ozcanyardimci/IoT_gateway/docs/subsystems/rs232.md

# RS232 Subsystem — Build Plan

**Status:** DONE, all 8 plan steps closed 2026-09-10. ERC deliberately not run before
closing the doc — project moved to a single end-of-project ERC pass across all
subsystems (Ozcan's decision, same approach `status-indication.md` already used) rather
than the per-subsystem pre-merge policy earlier subsystems followed. Tracked in
`CLAUDE.md` Open items.

## Scope

One point-to-point RS232 serial port on IOBOARD: TXD/RXD only, referenced to `GND_LOGIC`
(this port is **not** isolated — already fixed in `power.md`'s isolation table: "RS232 |
No | MAX3232E has no isolation"). No hardware flow control lines (RTS/CTS/DTR/DSR/etc.) —
same reasoning already applied project-wide: this project only ever wired TX/RX for its
UART-based interfaces. No DE/RE — that's an RS485-specific half-duplex control signal,
not applicable here. Not in scope: RS485 (separate subsystem, already complete), PCB
layout, DTE/DCE cable-adapter conventions for whatever gets plugged into the field side.

## Design approach

Four decisions, in the order they were made:

1. **Transceiver: TI MAX3232EIPWR (TSSOP-16, tape & reel, -40 to +85°C), one channel
   used.** Corrected 2026-09-10 from an earlier placeholder "MAX3232EI" that was never a
   real orderable part by itself — it's Texas Instruments' industrial-temp *family
   prefix*, not a buyable SKU (needs a package suffix: EID/EIDB/EIDW/EIPW, each with an
   optional R for tape-and-reel). Landed on TI's part specifically, not Analog
   Devices/Maxim's equivalent (MAX3232EEUE+), because TI's is the one with a ready
   SnapEDA symbol/footprint — practical, not electrical: pinout and function are
   identical either way, same classic second-sourced part. Datasheet switched to match:
   TI's own MAX3232E datasheet, not ADI/Maxim's. The MAX3232E family itself has been the
   standing choice for this project since before this doc existed (`architecture.md`,
   `power.md`) — a 3.3V-native RS232 transceiver, consistent with the `3V3_LOGIC` rail
   everything else on this board runs from. Full datasheet obtained and confirmed
   2026-09-10 ([TI MAX3232E
   datasheet](https://www.ti.com/lit/ds/slls664c/slls664c.pdf)): 16-pin part, two
   independent driver/receiver channels. This design only needs one RS232 signal pair
   (TXD/RXD), so channel 1 (DIN1/DOUT1, RIN1/ROUT1) is used; channel 2 (DIN2/DOUT2,
   RIN2/ROUT2) is left unconnected — same "spare, intentionally left unused" pattern
   already used for the analog subsystem's second op-amp unit.
2. **Charge-pump capacitors: 0.1µF x4, matching the 3.3V±0.3V operating row, plus a
   0.1µF VCC bypass cap.** Re-checked directly against TI's own "Table 3. VCC vs
   Capacitor Values" 2026-09-10: it actually has **three** rows, not two — 3.3V±0.3V
   (C1=0.1µF, C2/C3/C4=0.1µF), 5V±0.5V (C1=0.047µF, C2/C3/C4=0.33µF), and a third "3V to
   5.5V" extended-range row (C1=0.1µF, C2/C3/C4=0.47µF) meant for designs that need one
   fixed cap set across the whole supply range. This board's logic rail is `3V3_LOGIC`
   (3.15-3.45V per the rail's own spec, confirmed already in `power.md`), which sits
   squarely inside the 3.3V±0.3V row (3.0-3.6V) — so the 0.1µF set is still the correct
   pick; the earlier version of this decision just didn't mention the third row existed
   (didn't change which capacitors were selected). Cross-checked against the typical
   operating circuit (TI datasheet Figure 7), which shows C1/C2/C3/C4 all at 0.1µF plus a
   separate 0.1µF `CBYPASS` on VCC — confirms the reservoir caps (what this doc calls
   C2-C4) aren't all one part named "C2"; TI's figure genuinely has three separate
   reservoir/bypass capacitors at that value, matching the 5-capacitor count already used
   on the schematic (C24-C27, C29).
3. **Protection network: none added beyond the transceiver's own on-chip ESD + datasheet
   application circuit.** Considered, and decided against, a dedicated external TVS
   network (the same class of decision RS485 made *in favor of* — see below for why RS232
   comes out differently). Reasoning:
   - The datasheet's own recommended application circuit adds no external protection
     components at all — on-chip ESD alone (±15kV HBM, ±15kV IEC1000-4-2 air-gap, ±8kV
     IEC1000-4-2 contact discharge, all on the RS232 I/O pins) is what the manufacturer
     designed this part to rely on.
   - The receiver inputs are separately rated to ±25V absolute maximum, safe even with
     the part fully unpowered (VCC = 0) — this already covers the great majority of
     realistic miswiring scenarios directly, without needing an add-on component.
   - **Reference-design evidence (2026-09-10):** photos of the reference hardware
     teardown's assembled enclosure show its RS485 subsystem got a dedicated
     protection stage (matches the harsh-environment protection network `rs485.md`
     already selected from the transceiver's own manufacturer reference circuit), but no
     equivalent added protection stage was visible anywhere for the RS232 port — same
     connector-panel footprint, same terminal-block style, no extra populated components
     nearby that would suggest a GDT/TVS/choke network specific to that port. RS485 is a
     bus interface meant for long cable runs near industrial equipment (motors, VFDs,
     contactors) — a genuinely different exposure profile from a short point-to-point
     RS232 link, which is consistent with the two subsystems landing on different
     protection tiers.
   - **Residual risk, flagged rather than silently accepted:** this project reuses one
     Phoenix Contact terminal-block connector family across every subsystem, including
     the 10-30VDC field power input — so a miswired field-power connector landing on this
     3-position RS232 terminal block is physically possible, and the field range's high
     end (up to 30V) exceeds the receiver's ±25V absolute maximum by up to 5V. A TVS
     wouldn't actually close this specific gap well: TVS diodes are pulse-rated
     (transient energy), not continuous-dissipation-rated, so a *sustained* 24-30VDC
     fault would overwhelm a small TVS's continuous power handling in roughly the same
     way it would overwhelm the transceiver's own rating — it would likely fail (ideally
     open, but not guaranteed) rather than indefinitely protect the port. Given that, and
     given the reference design's own apparent choice not to add one here, the mitigation
     for this residual risk is procedural, not componentry: clear panel silkscreen
     labeling per connector position (already this project's practice) rather than an
     add-on part that wouldn't reliably solve the sustained-miswiring case anyway. If a
     real deployment or bench test ever shows this gap actually matters in practice, it's
     revisitable — nothing here is a one-way door (the terminal block's physical footprint
     has room for a future TVS if one gets added later).
4. **Connector: reuse Phoenix Contact MC 1,5/3-ST-3,5 (MPN 1840379), same part already
   used for RS485's connector.** 3 positions: TXD, RXD, GND. 3.5mm pitch, 28-16AWG
   (1.5mm²) screw terminals, through-hole pluggable — matches J1-J5's family for
   BOM/part-count consistency. **Reference-design evidence (2026-09-10):** the reference
   hardware teardown's enclosure connector panel shows RS232 using the same small
   rectangular terminal-block-style cutout as RS485, Analog I/O, and the power input —
   not a D-sub/DB9 shape — confirming a pluggable terminal block, not a DB9 connector, is
   the reference design's actual choice for this port. This resolves the DB9-vs-terminal-
   block fork from this doc's original AskUserQuestion in favor of terminal block, and
   the family/MPN was already locked project-wide, so no new part number is added to the
   BOM baseline (same 1840379 as RS485's connector).

## Step 1 results: front end (locked, 2026-09-10)

| Parameter | Value | Source |
|---|---|---|
| Transceiver | TI MAX3232EIPWR (TSSOP-16, tape & reel) | [TI MAX3232E datasheet](https://www.ti.com/lit/ds/slls664c/slls664c.pdf), full PDF obtained 2026-09-10; exact orderable part confirmed 2026-09-10 (see decision 1 — earlier "MAX3232EI" was not a real SKU) |
| Supply | 3.0-5.5V, 0.3mA typ / 1mA max supply current (no load, VCC=3.3V or 5V) | Datasheet — already matches `power.md`'s existing MAX3232E row exactly |
| Max data rate | 150kbit/s min (guaranteed worst-case) / 250kbit/s max, RL=3kΩ CL=1000pF | Datasheet Switching Characteristics table — re-verified 2026-09-10: **150kbit/s is the guaranteed minimum, 250kbit/s is the max column, not a guaranteed floor** (this doc's earlier framing had it backwards, see revision history) |
| Channels used | 1 of 2 (T1/R1); T2/R2 left unconnected, spare | This design only needs one RS232 signal pair |
| Charge-pump caps | C1 (flying) = 0.1µF; C2, C3, C4 (reservoir/bypass) = 0.1µF each | Datasheet's "Table 3. VCC vs Capacitor Values," 3.3V±0.3V row, matched against `3V3_LOGIC` |
| VCC bypass cap | 0.1µF, VCC to GND — separate from the four charge-pump caps above | Datasheet's typical operating circuit, Figure 7 (`CBYPASS`) |
| On-chip ESD (RS232 I/O pins) | ±15kV HBM, ±15kV IEC1000-4-2 air-gap, ±8kV IEC1000-4-2 contact discharge | Datasheet — re-confirmed 2026-09-10 |
| Receiver input absolute max | ±25V, safe even with VCC = 0 (unpowered) | Datasheet — re-confirmed 2026-09-10 |
| Driver output swing (into 3kΩ) | High 5-5.4V, Low -5 to -5.4V | Datasheet |
| Receiver thresholds @ VCC=3.3V | VIT- (low) 0.6-1.2V, VIT+ (high) 1.5-2.4V; 0.3V hysteresis | Datasheet — re-verified 2026-09-10 against the exact Electrical Characteristics table: this doc's first pass had the low threshold as 0.6-1.1V and hysteresis as 0.5V, both wrong (real values 0.6-1.2V and 0.3V) — corrected here, see revision history |

**Full pinout** (TI's datasheet, D/DW/DB/PW packages — confirmed 2026-09-10). This
replaces an earlier pull from ADI/Maxim's pin-description table, which had VCC and GND
on the *opposite* pins (15=VCC/16=GND there vs. 15=GND/16=VCC here) — a real correction,
not a cosmetic one, since VCC/GND is exactly the kind of thing you don't want backwards
on the board. Now that the part being used is TI's specifically, this table is TI's own
pin numbering, single-sourced, not cross-checked against a second manufacturer's diagram.

| Pin | Mark | Function |
|---|---|---|
| 1 | C1+ | Charge-pump flying capacitor positive |
| 2 | V+ | Positive charge pump output |
| 3 | C1- | Charge-pump flying capacitor negative |
| 4 | C2+ | Charge-pump flying capacitor positive |
| 5 | C2- | Charge-pump flying capacitor negative |
| 6 | V- | Negative charge pump output |
| 7 | DOUT2 | RS232-side transmit output, channel 2 — unused |
| 8 | RIN2 | RS232-side receive input, channel 2 — unused |
| 9 | ROUT2 | Logic-side receive output, channel 2 — unused |
| 10 | DIN2 | Logic-side transmit input, channel 2 — unused |
| 11 | DIN1 | Logic-side transmit input, channel 1 — from MCU TXD |
| 12 | ROUT1 | Logic-side receive output, channel 1 — to MCU RXD |
| 13 | RIN1 | RS232-side receive input, channel 1 — from field TXD |
| 14 | DOUT1 | RS232-side transmit output, channel 1 — to field RXD |
| 15 | GND | Ground |
| 16 | VCC | 3.0-5.5V supply |

## Step 2 results: protection (decided, 2026-09-10)

No dedicated protection network added — see decision 3 above for the full reasoning
(datasheet's own application circuit, ±25V-safe-unpowered receiver rating, and the
reference design's own apparent choice not to add a protection stage for this port).
Nothing to select or spec here; this step closes with "none" as the deliberate answer,
same as decision 2 in `rs485.md` closed with "no termination network" as its deliberate
answer.

## Step 3 results: connector (locked, 2026-09-10)

**Phoenix Contact MC 1,5/3-ST-3,5** (MPN 1840379) — same part already used for J5 (RS485).
3 positions: TXD, RXD, GND. Rated 8A/160V, heavy overkill for signal-level current, kept
anyway for BOM/part-family consistency, same reasoning already used project-wide.

**Schematic symbol (confirmed 2026-09-10 by checking `rs485.kicad_sch` directly):** this
project places connectors using KiCad's built-in `Connector_Generic:Conn_01x03` symbol,
not a manufacturer-specific one — footprint left blank until the pre-merge footprint
pass, same as J5. Pin assignment: pin 1 = TXD (to DOUT1), pin 2 = RXD (from RIN1), pin 3
= `GND_LOGIC`.

## Step 4 results: schematic capture (done, 2026-09-10)

Captured in `hardware/kicad/ioboard/ioboard/rs232.kicad_sch` and wired into the root
sheet (`ioboard.kicad_sch`, page 7). Verified directly against the saved file content
(not just the on-screen schematic), pin-by-pin against decision 1's pinout table:

- U16 (MAX3232EIPWR): all 16 pins present. DIN1 (pin 11) ← hierarchical label
  `RS232_TXD` (input); ROUT1 (pin 12) → hierarchical label `RS232_RXD` (output) — got
  the shape right this time, unlike `rs485.md`'s still-open `RS485_RXD` mistake. VCC
  (pin 16) → `3V3_LOGIC`; GND (pin 15) → `GND_LOGIC` global label directly. Channel 2
  pins (DIN2/10, DOUT2/7, RIN2/9→ROUT2, RIN2/8) all carry explicit `no_connect` flags —
  clean on channel 2, not just silently left floating.
- Capacitors: C24 across C1+/C1- (flying cap), C25 across C2+/C2- (reservoir cap), C27
  from V- to `GND_LOGIC`, C29 from V+ to `GND_LOGIC`, C26 from VCC/`3V3_LOGIC` to
  `GND_LOGIC` (the bypass cap) — all 5 at 0.1µF, matching Step 1's table exactly.
- J6 (`Connector_Generic:Conn_01x03`, blank footprint, same convention as J5): pin 1 =
  local label `TXD` (from DOUT1), pin 2 = local label `RXD` (to RIN1), pin 3 =
  `GND_LOGIC` — matches decision 4's pin assignment.
- **Root-sheet integration caught and fixed:** the `rs232` sheet block was initially
  added to `ioboard.kicad_sch` with zero sheet pins — the same class of gap that caused
  the RS485 root-sheet incident earlier this subsystem cycle (there it was a full
  regression/data loss; here it was just never done yet). Caught during verification,
  fixed by adding the 3 sheet pins (`3V3_LOGIC` input, `RS232_TXD` input, `RS232_RXD`
  output) via KiCad's Import Sheet Pins, matching the child sheet's hierarchical labels
  exactly — confirmed correct on re-check.

## Step 5: verification checklist / ERC — deferred to end-of-project pass

Not run. Superseded the per-subsystem pre-merge ERC policy used for earlier subsystems:
Ozcan's decision 2026-09-10 is to run ERC once, project-wide, after every subsystem's
connections are done, rather than per-subsystem before each merge — same approach
`status-indication.md` already used. Tracked as an open item in `CLAUDE.md`, not a gap
in this doc closing out.

## Step 6: acceptance criteria (confirmed, 2026-09-10)

1. Logic-side operation from `3V3_LOGIC` (3.15-3.45V) draws current within the ~0.3mA
   typ / 1mA max already accounted for in `power.md`'s 3.3V-LOGIC rail sizing — no change
   needed there (already itemized as its own row).
2. TXD/RXD levels meet RS232 spec at the connector: driver output 5-5.4V high / -5 to
   -5.4V low into a 3kΩ load, receiver correctly detects incoming signals per datasheet
   thresholds (VIT- 0.6-1.2V, VIT+ 1.5-2.4V, 0.3V hysteresis).
3. Port survives being driven by another compliant RS232 device presenting the full
   legitimate ±15V signal swing (EIA/TIA-232 spec range) without damage or misdetection —
   covered by the receiver's ±25V absolute-max rating with margin.
4. The residual miswiring gap (field-power's 30V high end vs. the receiver's ±25V
   absolute max) remains a known, documented, non-blocking risk per decision 3 — not
   something this step needs to close, since it was deliberately accepted rather than
   overlooked.
5. Communication is reliable at whatever baud rate the firmware actually configures, up
   to the datasheet's 150kbit/s guaranteed-minimum data rate (the datasheet's 250kbit/s
   figure is the max/best-case column, not a floor — don't design firmware timing against
   250kbit/s as if it were guaranteed) — bench item, can't be closed on paper.

Items 2, 3, and 5 require real hardware to close out fully — Rev-A bring-up.

## Step 7: documentation & BOM (done, 2026-09-10)

`hardware/datasheets/README.md` has an RS232 subsystem section (added alongside this
doc's earlier revisions). `hardware/bom/rs232_bom.csv` written with the real reference
designators from the closed schematic: U16, C24, C25, C26, C27, C29, J6.

## Step 8: sign-off (2026-09-10)

All 8 steps closed. RS232 schematic capture done and verified against this doc's locked
spec (Step 4). Remaining before board fab: real footprints (J6 currently blank, matching
project convention of deferring footprint assignment to the layout stage), and the
project-wide ERC pass (Step 5, deferred by design — see above).

## Steps

1. **Front end: transceiver, charge-pump capacitors** — **DONE (this doc)**.
2. **Protection** — **DONE (this doc)** — deliberately none added, see decision 3.
3. **Connector selection** — **DONE (this doc)** — Phoenix Contact MC 1,5/3-ST-3,5,
   reusing RS485's part number.
4. **Schematic capture (KiCad)** — **DONE**, verified against the locked spec pin-by-pin;
   root-sheet integration gap caught and fixed.
5. **Verification checklist / ERC** — Deferred to a single end-of-project pass across all
   subsystems (Ozcan's decision, superseding the earlier per-subsystem pre-merge policy).
6. **Acceptance criteria** — **DONE (this doc)**, confirmed now that Step 4 is closed.
7. **Documentation & BOM** — **DONE** — `hardware/bom/rs232_bom.csv` written,
   `hardware/datasheets/README.md` updated.
8. **Sign-off** — **DONE**.

## Revision history

| Date | Change |
|---|---|
| 2026-09-10 | Doc created. Step 1 (front end) locked from the full MAX3232E datasheet (ADI/Maxim MAX3222E-MAX3246E family PDF). Step 2 (protection) decided as "none added," reasoning documented in decision 3 — datasheet's own application circuit, the receiver's ±25V-safe-unpowered rating, and reference-design photo evidence showing no dedicated protection stage for this port (unlike RS485). Step 3 (connector) locked as a reuse of RS485's Phoenix Contact MC 1,5/3-ST-3,5 (MPN 1840379), resolving the original DB9-vs-terminal-block open question in favor of terminal block — confirmed from reference-hardware teardown photos showing the same terminal-block-style connector-panel cutout used for RS232 as for RS485 and Analog I/O, not a D-sub shape. Step 4 guidance written proactively to avoid repeating `rs485.md`'s `RS485_RXD` label-shape mistake. |
| 2026-09-10 | **Correction, same day.** "MAX3232EI" (used throughout this doc's first pass) was never a real orderable part — it's Texas Instruments' industrial-temp family prefix, not a buyable SKU. Corrected to TI MAX3232EIPWR (TSSOP-16, tape & reel) — picked over the ADI/Maxim equivalent (MAX3232EEUE+) because TI's has a ready SnapEDA symbol/footprint. Datasheet switched to TI's own PDF to match. This surfaced a real pin-numbering error: TI's part has GND on pin 15 and VCC on pin 16 — the opposite of what the earlier ADI/Maxim-sourced pinout table had. Full pinout table rebuilt from TI's datasheet with TI's pin names (DIN1/DOUT1/RIN1/ROUT1 instead of T1IN/T1OUT/R1IN/R1OUT) — same functions, different manufacturer's naming. Step 4 guidance updated to match. |
| 2026-09-10 | Schematic capture done (Step 4) and verified pin-by-pin against the locked spec — all correct. Root-sheet integration was initially incomplete (the `rs232` sheet block existed in `ioboard.kicad_sch` with zero sheet pins), caught during verification and fixed by adding the 3 sheet pins with correct shapes (`RS232_RXD` as output, avoiding `rs485.md`'s open shape bug). Step 5 (ERC) reclassified from "deferred to pre-merge" to "deferred to a single end-of-project pass" — Ozcan's decision, applies going forward, matching `status-indication.md`'s existing approach. Steps 6-8 closed: acceptance criteria confirmed, `hardware/bom/rs232_bom.csv` written, doc signed off. All 8 steps now DONE. |
| 2026-09-23 | **Pin-assigned to real MCU GPIOs (roadmap step 6).** `RS232_TXD`/`RS232_RXD` now carry hierarchical labels wired to `core-compute.kicad_sch`: TXD→GPIO5, RXD→GPIO6. Neither pin has any special/strapping function per Espressif's datasheet — no caveats. Full pin table in `docs/architecture.md`. |
| 2026-09-10 | **Re-verification pass, requested before commit.** Re-fetched TI's datasheet three separate times with narrow, literal-quote prompts (not relying on the earlier session's single pull) and found: (1) receiver low threshold was recorded as 0.6-1.1V, actual is 0.6-1.2V; (2) hysteresis was recorded as 0.5V, actual is 0.3V — both corrected in Step 1's table and acceptance criterion 2; (3) the "250kbps guaranteed worst-case" data-rate framing had it backwards — 250kbit/s is the datasheet's MAX/best-case column, 150kbit/s is the actual guaranteed minimum; corrected in Step 1's table and acceptance criterion 5, since firmware baud-rate margin should be planned against 150kbit/s, not 250kbit/s; (4) decision 2's capacitor-selection table description only mentioned two supply-voltage rows (3.0-3.6V / 4.5-5.5V) — TI's actual "Table 3" has three rows, including a "3V to 5.5V extended range" row not previously mentioned; doesn't change which capacitors were picked (3V3_LOGIC still lands in the 3.3V±0.3V row), just fixed for completeness; (5) decision 1 still used ADI/Maxim's old pin-naming (T1IN/T1OUT/R1IN/R1OUT) in one paragraph left over from before the TI switch — corrected to TI's DIN1/DOUT1/RIN1/ROUT1 for consistency with the rest of the doc. Everything else independently re-checked and confirmed unchanged: full pinout table, ESD ratings, receiver ±25V/unpowered-safe rating, supply current, driver output swing, and the Phoenix Contact MC 1,5/3-ST-3,5 connector's 8A/160V rating (checked directly against Phoenix Contact's own product page, not just a distributor listing — one distributor's page showed a conflicting 320V figure, not used here). |
