ozcanyardimci/IoT_gateway/reference-photos/2026-09-08-hardware-assembly-photos/photo_01_993a01e6.jpg

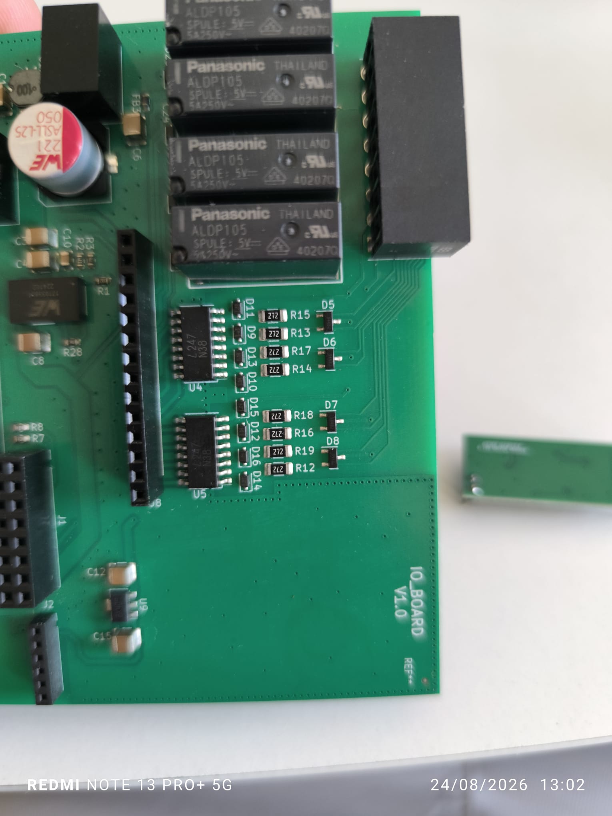
reference-photos/2026-09-08-hardware-assembly-photos/photo_01_993a01e6.jpg
