ozcanyardimci/IoT_gateway/reference-photos/2026-09-08-hardware-assembly-photos/photo_03_f79ddcff.jpg

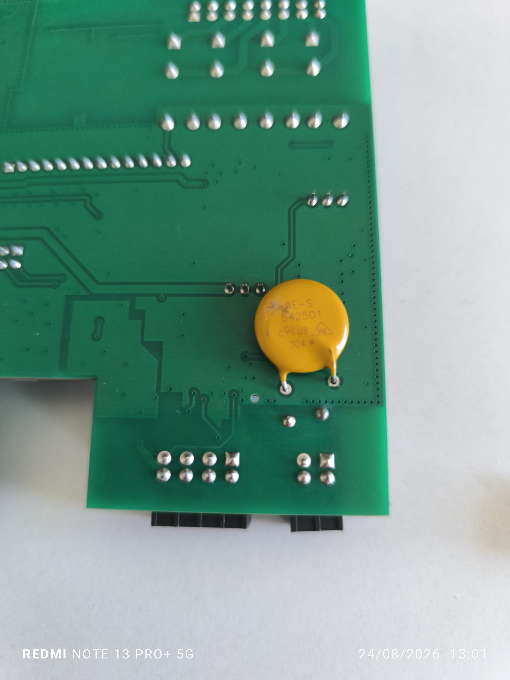
reference-photos/2026-09-08-hardware-assembly-photos/photo_03_f79ddcff.jpg
