ozcanyardimci/IoT_gateway/reference-photos/2026-09-08-hardware-assembly-photos/photo_05_fe951f44.jpg

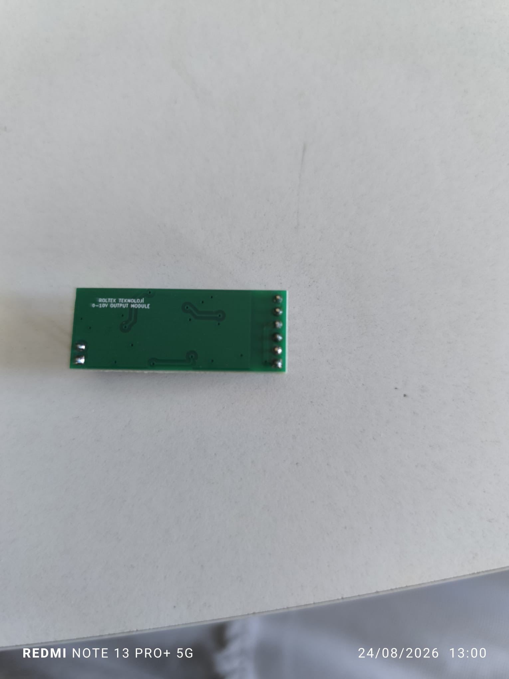
reference-photos/2026-09-08-hardware-assembly-photos/photo_05_fe951f44.jpg
