ozcanyardimci/IoT_gateway/reference-photos/2026-09-08-hardware-assembly-photos/photo_06_ef9526c5.jpg

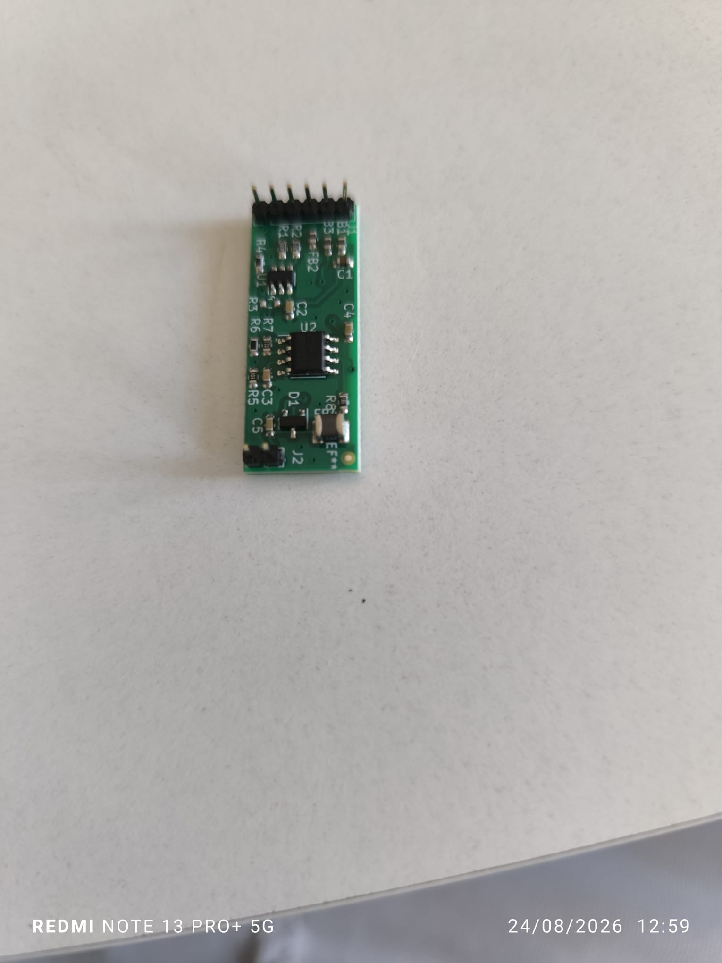
reference-photos/2026-09-08-hardware-assembly-photos/photo_06_ef9526c5.jpg
