ozcanyardimci/IoT_gateway/reference-photos/2026-09-08-hardware-assembly-photos/photo_08_b16dd279.jpg

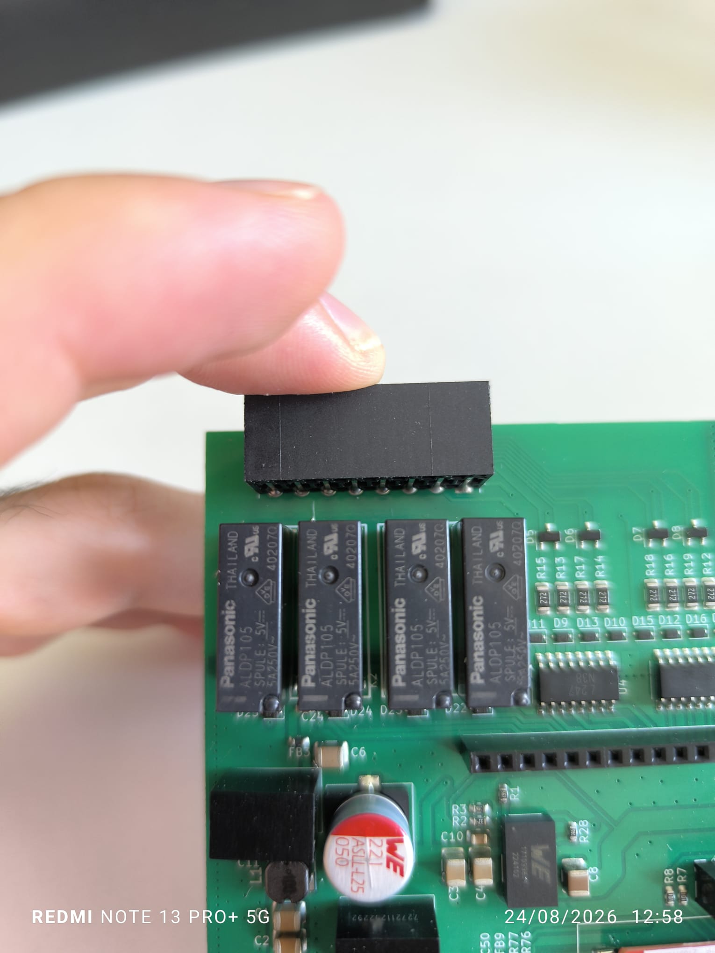
reference-photos/2026-09-08-hardware-assembly-photos/photo_08_b16dd279.jpg
