ozcanyardimci/IoT_gateway/reference-photos/2026-09-08-hardware-assembly-photos/photo_10_7394d056.jpg

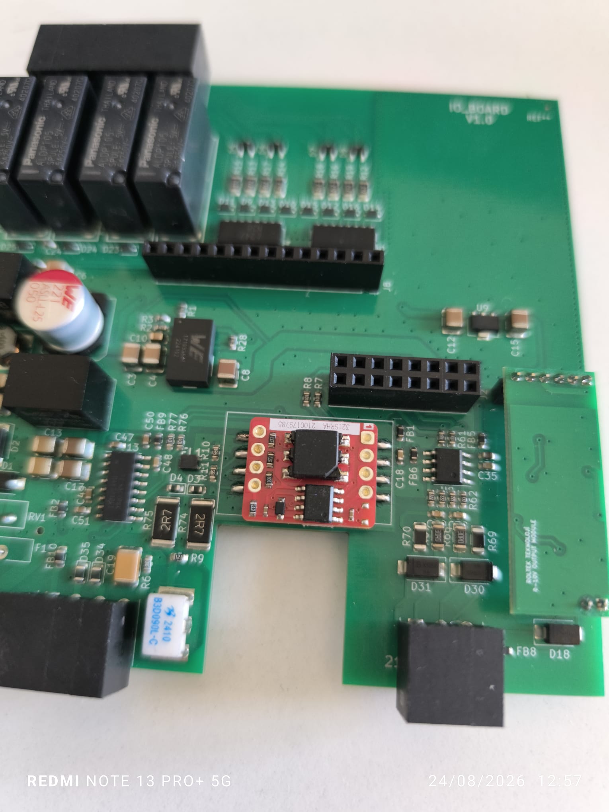
reference-photos/2026-09-08-hardware-assembly-photos/photo_10_7394d056.jpg
