ozcanyardimci/IoT_gateway/reference-photos/2026-09-08-hardware-assembly-photos/photo_11_28bd200a.jpg

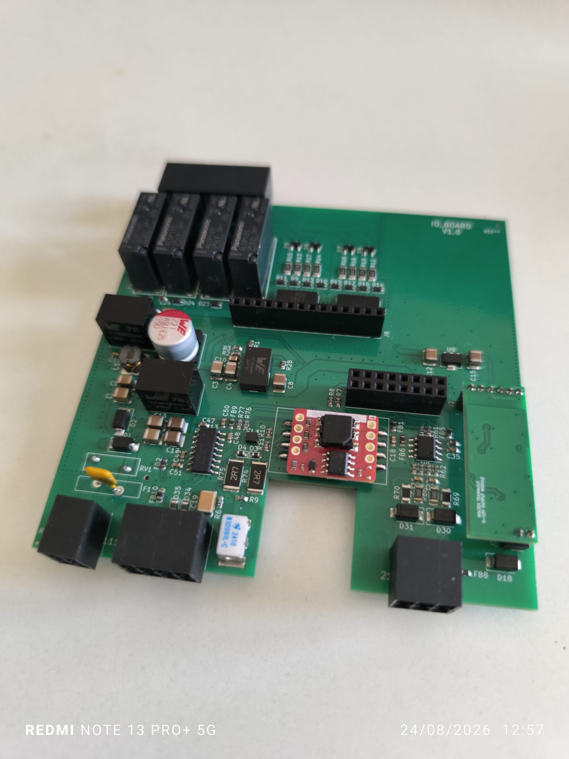
reference-photos/2026-09-08-hardware-assembly-photos/photo_11_28bd200a.jpg
