ozcanyardimci/IoT_gateway/reference-photos/2026-09-08-hardware-assembly-photos/photo_12_bba23080.jpg

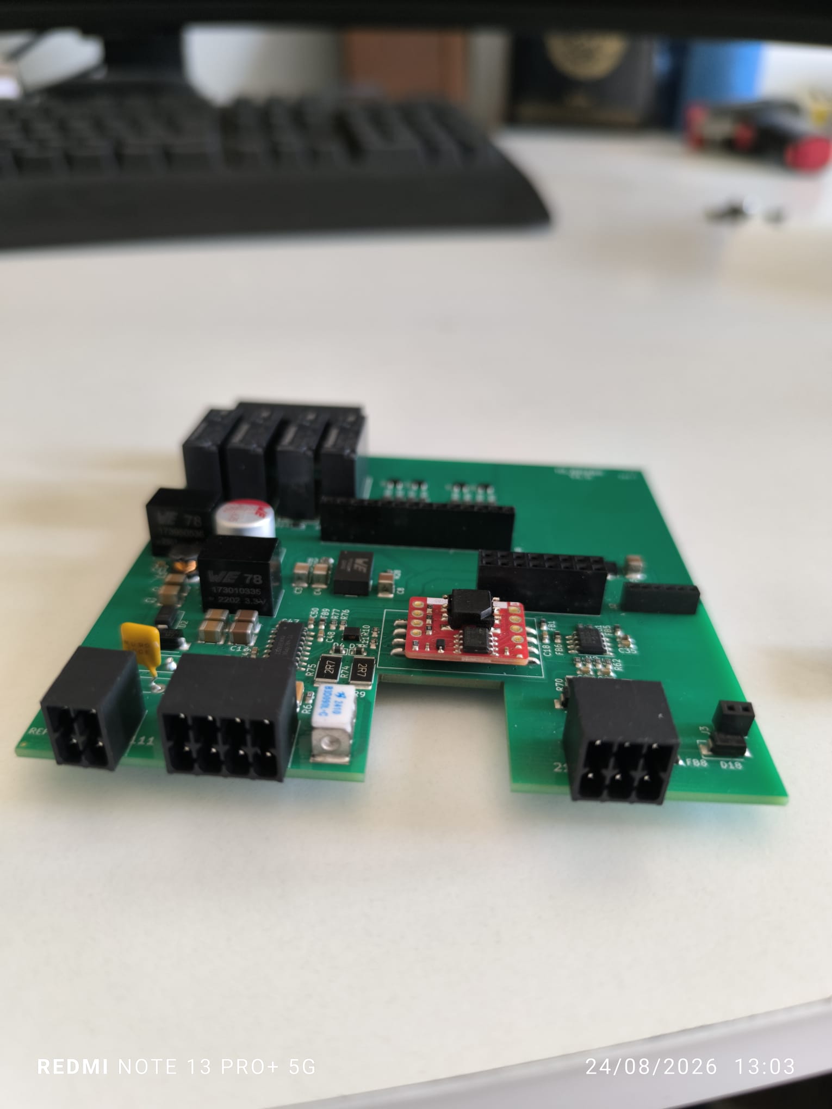
reference-photos/2026-09-08-hardware-assembly-photos/photo_12_bba23080.jpg
