ozcanyardimci/IoT_gateway/reference-photos/2026-09-08-hardware-assembly-photos/photo_13_034e32e1.jpg

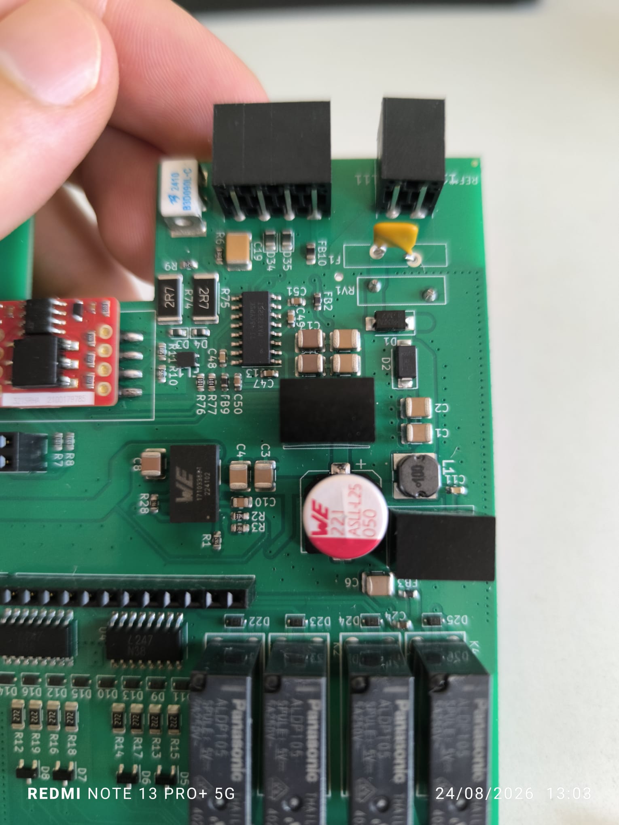
reference-photos/2026-09-08-hardware-assembly-photos/photo_13_034e32e1.jpg
