ozcanyardimci/IoT_gateway/reference-photos/2026-09-08-hardware-assembly-photos/photo_14_53fe1a50.jpg

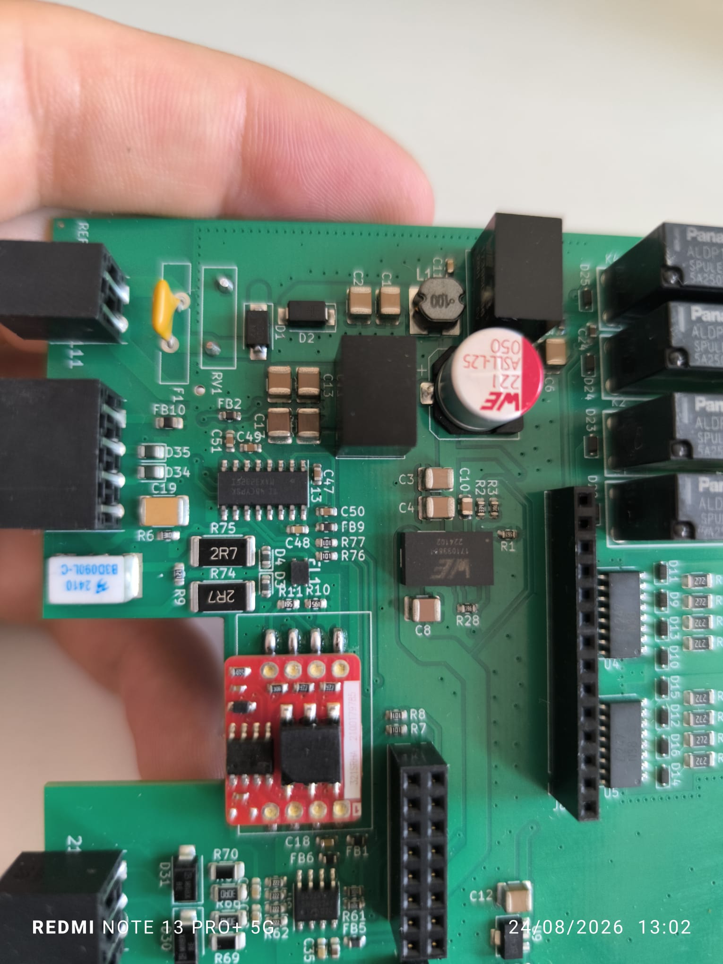
reference-photos/2026-09-08-hardware-assembly-photos/photo_14_53fe1a50.jpg
