ozcanyardimci/IoT_gateway/reference-photos/2026-09-08-hardware-assembly-photos/photo_15_20eb996b.jpg

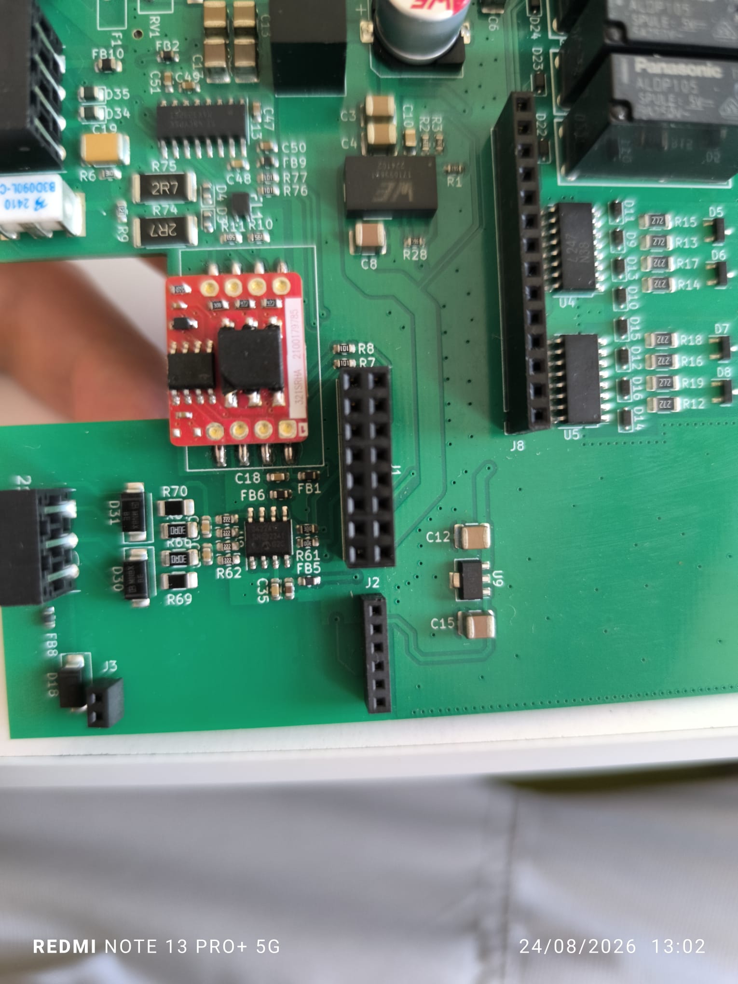
reference-photos/2026-09-08-hardware-assembly-photos/photo_15_20eb996b.jpg
