ozcanyardimci/IoT_gateway/reference-photos/2026-09-08-hardware-assembly-photos/photo_16_57c8dbfa.jpg

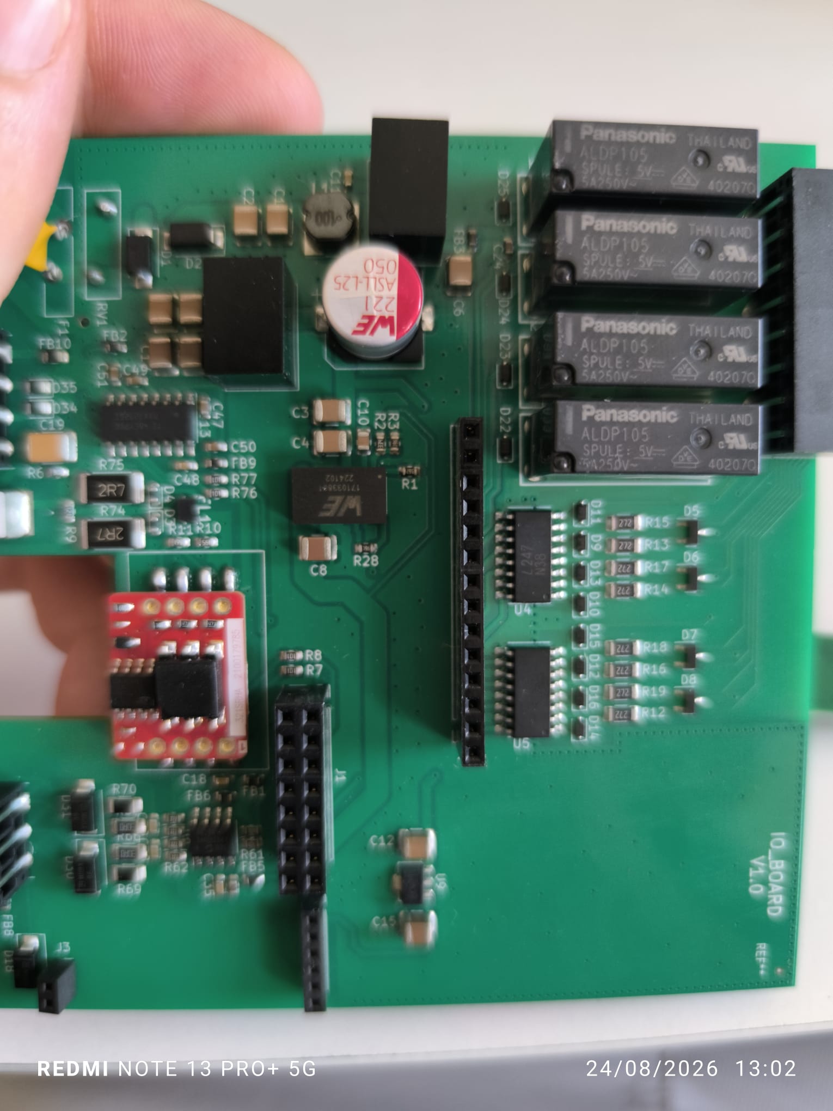
reference-photos/2026-09-08-hardware-assembly-photos/photo_16_57c8dbfa.jpg
