ozcanyardimci/IoT_gateway/reference-photos/2026-09-08-hardware-assembly-photos/photo_17_680f4264.jpg

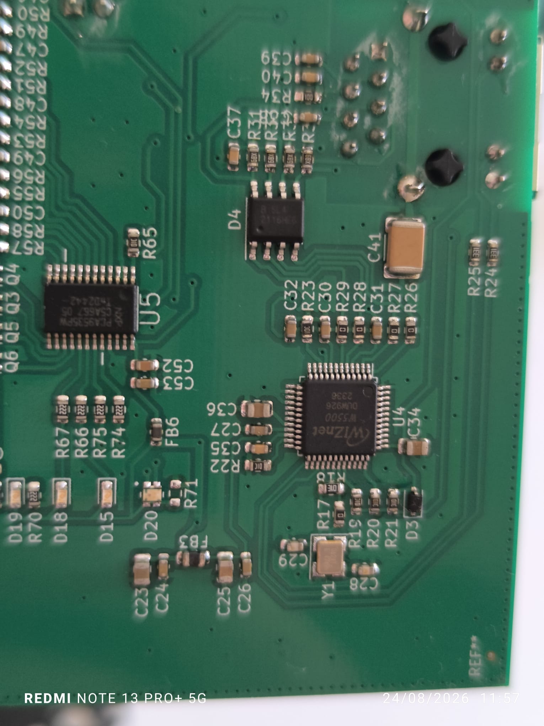
reference-photos/2026-09-08-hardware-assembly-photos/photo_17_680f4264.jpg
