ozcanyardimci/IoT_gateway/reference-photos/2026-09-08-hardware-assembly-photos/photo_19_8fbdda39.jpg

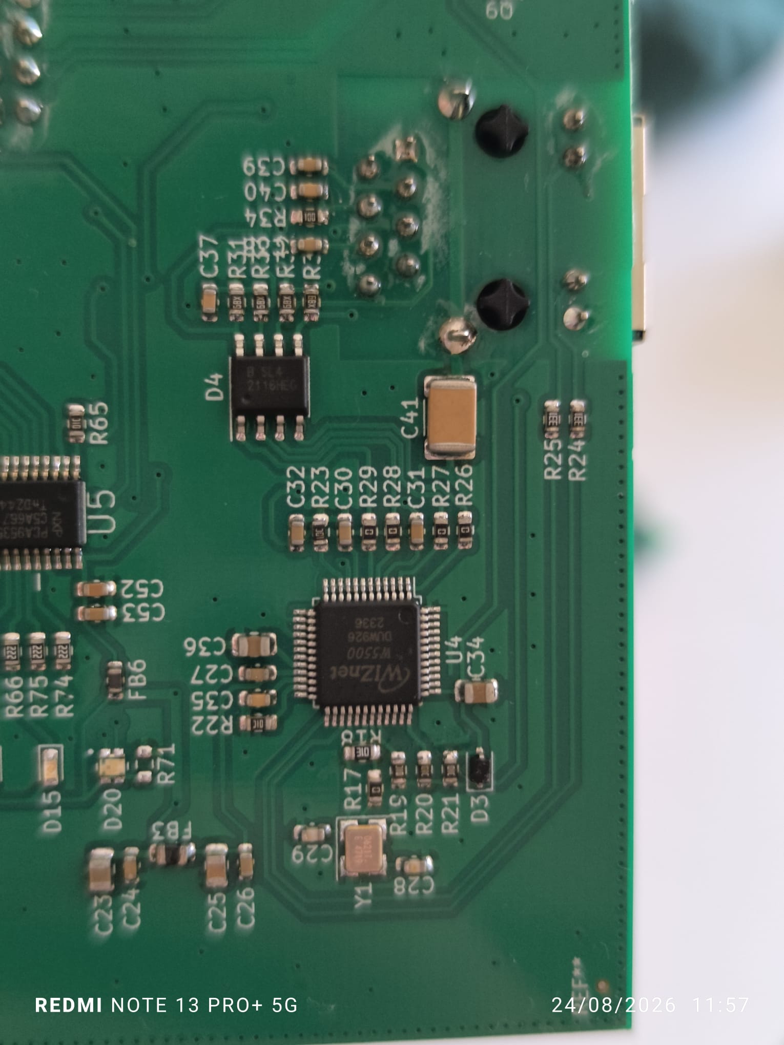
reference-photos/2026-09-08-hardware-assembly-photos/photo_19_8fbdda39.jpg
