ozcanyardimci/IoT_gateway/reference-photos/2026-09-08-hardware-assembly-photos/photo_20_057d9fcc.jpg

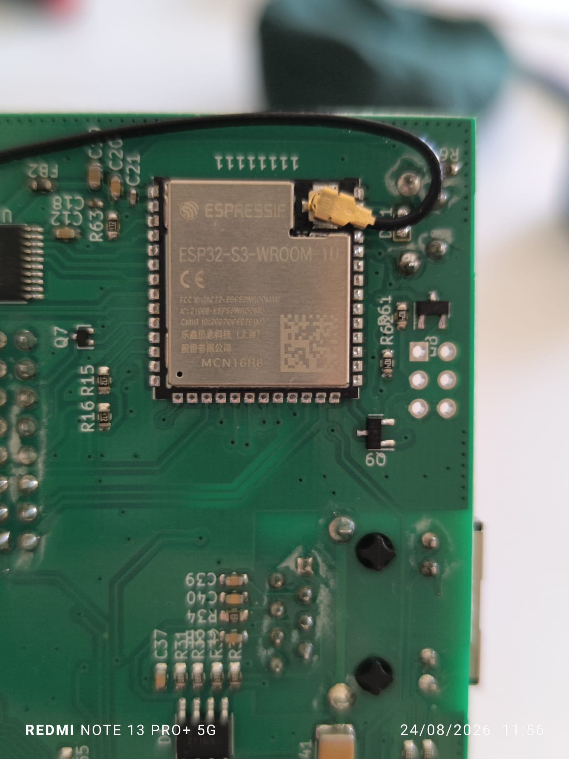
reference-photos/2026-09-08-hardware-assembly-photos/photo_20_057d9fcc.jpg
