ozcanyardimci/IoT_gateway/reference-photos/2026-09-08-hardware-assembly-photos/photo_21_51380d29.jpg

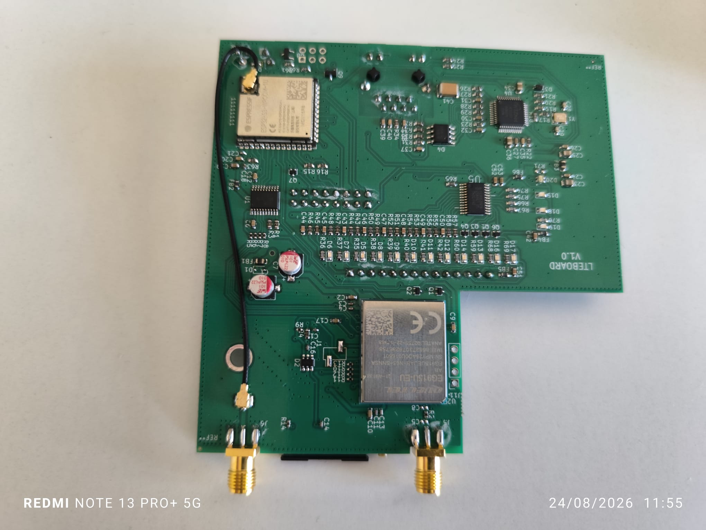
reference-photos/2026-09-08-hardware-assembly-photos/photo_21_51380d29.jpg
