ozcanyardimci/IoT_gateway/reference-photos/2026-09-08-hardware-assembly-photos/photo_22_46c99ca9.jpg

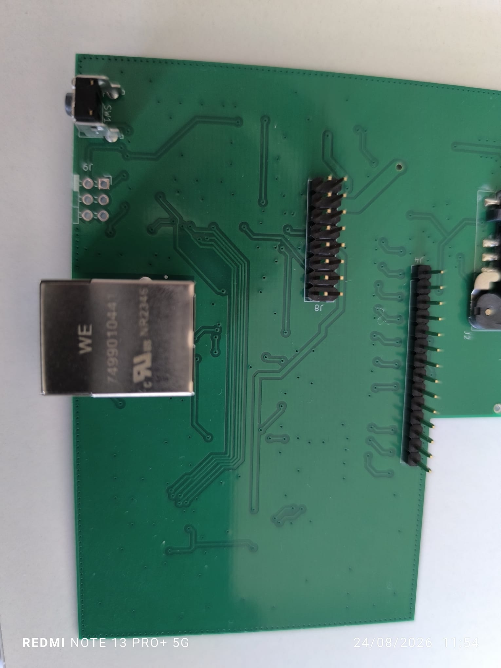
reference-photos/2026-09-08-hardware-assembly-photos/photo_22_46c99ca9.jpg
