ozcanyardimci/IoT_gateway/reference-photos/2026-09-08-hardware-assembly-photos/photo_23_e496ca2c.jpg

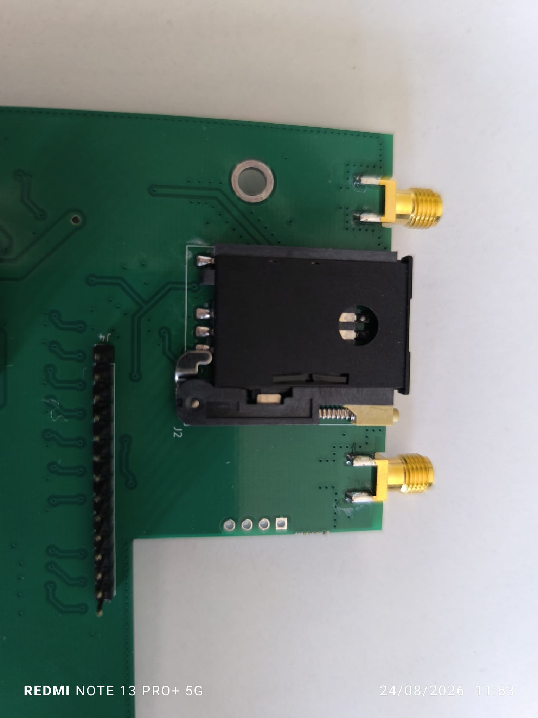
reference-photos/2026-09-08-hardware-assembly-photos/photo_23_e496ca2c.jpg
