ozcanyardimci/IoT_gateway/reference-photos/2026-09-08-hardware-assembly-photos/photo_24_a6faa21f.jpg

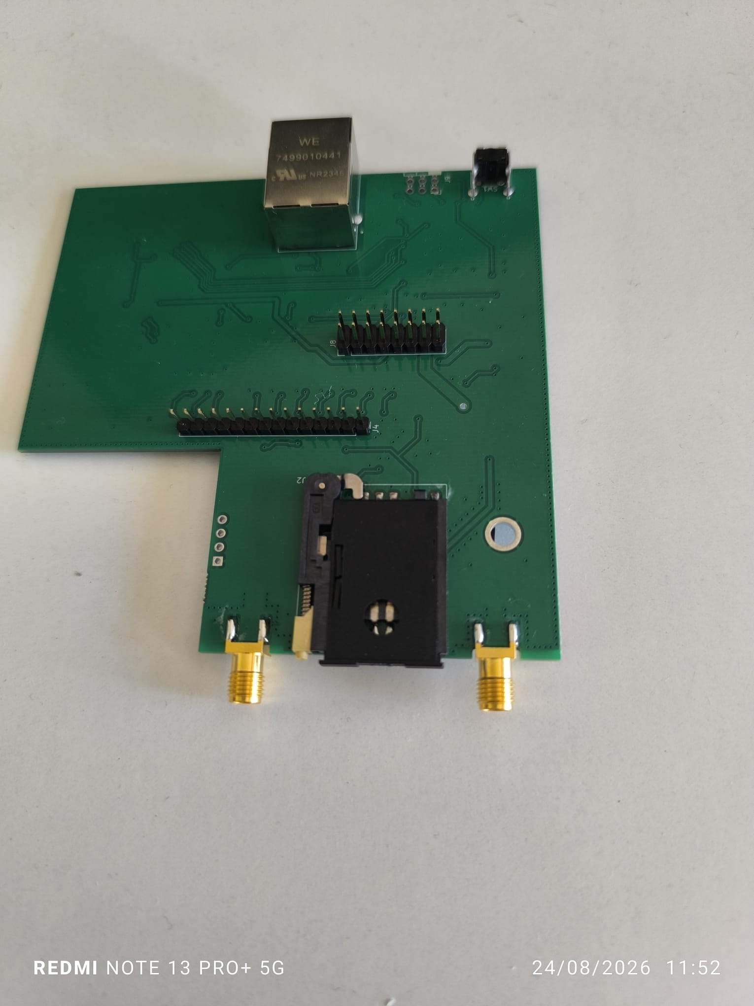
reference-photos/2026-09-08-hardware-assembly-photos/photo_24_a6faa21f.jpg
