ozcanyardimci/IoT_gateway/reference-photos/2026-09-08-hardware-assembly-photos/photo_25_f8faf6fd.jpg

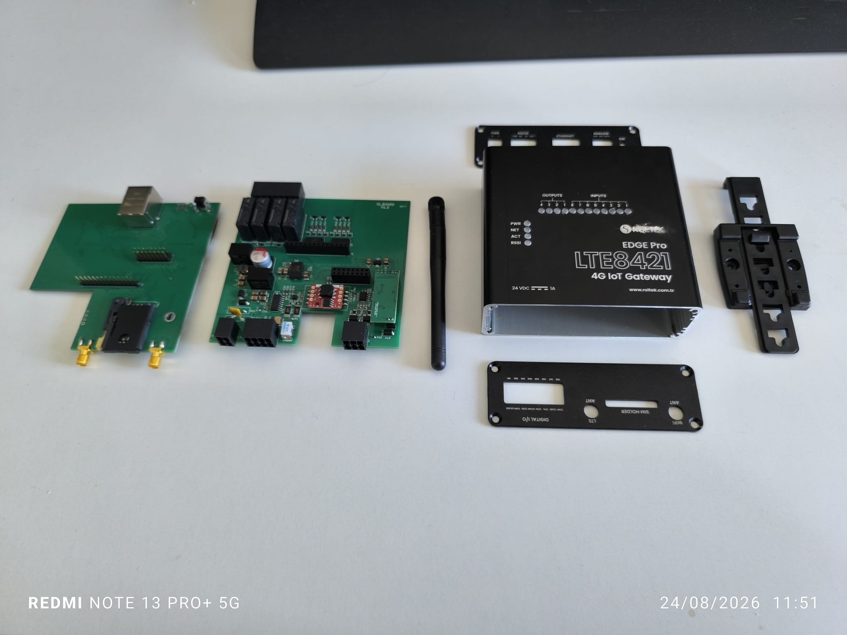
reference-photos/2026-09-08-hardware-assembly-photos/photo_25_f8faf6fd.jpg
