ozcanyardimci/IoT_gateway/reference-photos/2026-09-08-hardware-assembly-photos/photo_26_3b0e7860.jpg

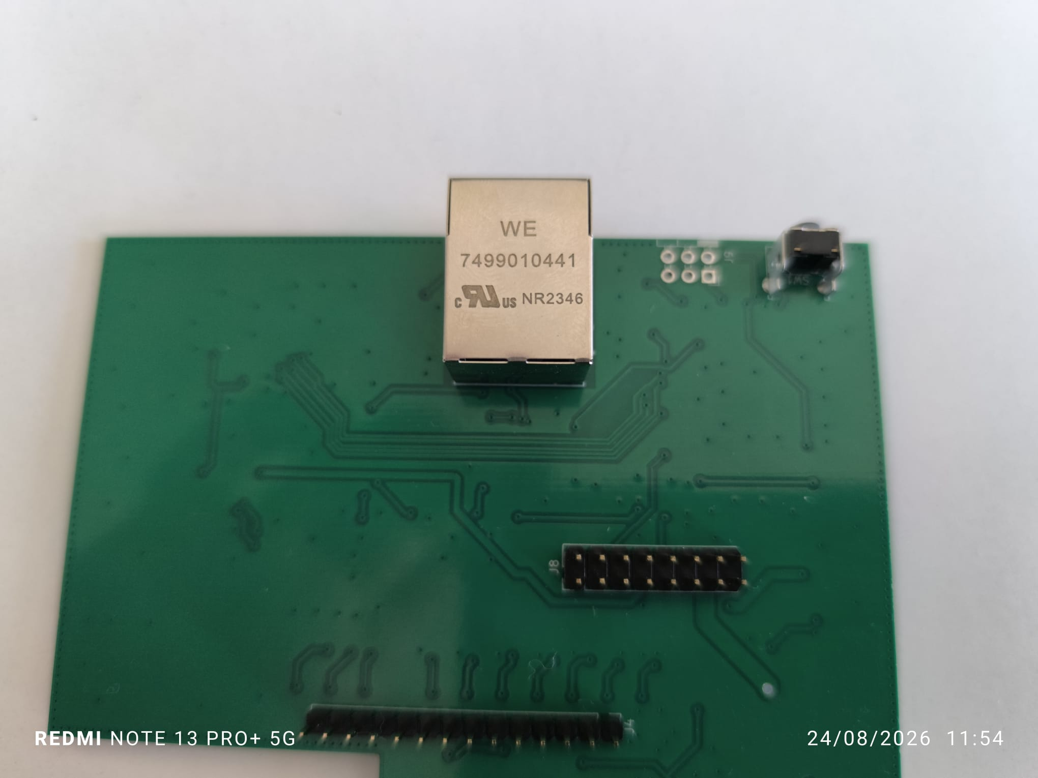
reference-photos/2026-09-08-hardware-assembly-photos/photo_26_3b0e7860.jpg
