ozcanyardimci/IoT_gateway/reference-photos/2026-09-08-hardware-assembly-photos/photo_27_6b47215a.jpg

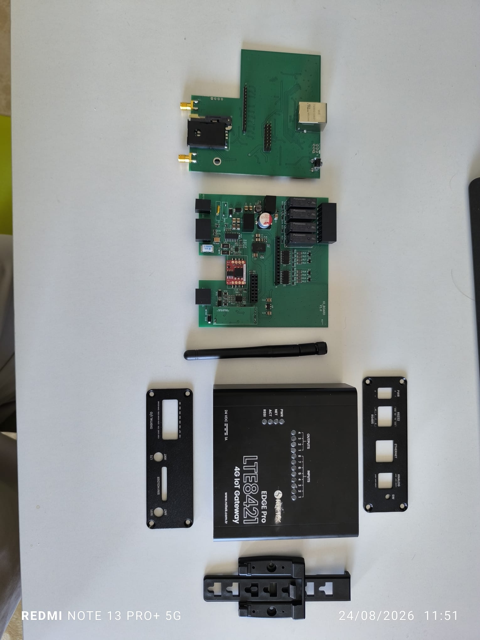
reference-photos/2026-09-08-hardware-assembly-photos/photo_27_6b47215a.jpg
