ozcanyardimci/IoT_gateway/reference-photos/2026-09-08-hardware-assembly-photos/photo_28_1c4159d3.jpg

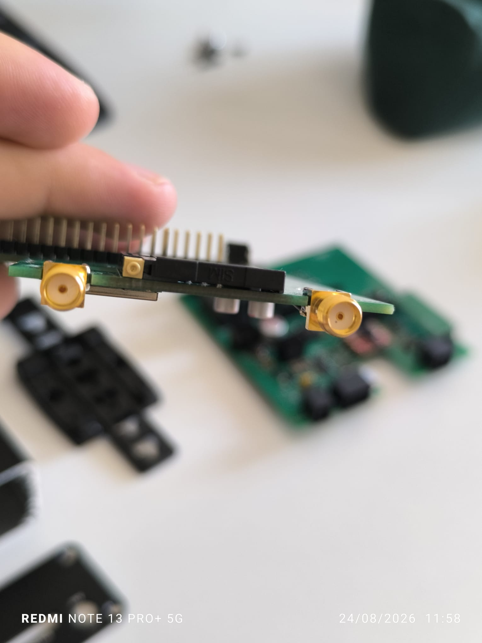
reference-photos/2026-09-08-hardware-assembly-photos/photo_28_1c4159d3.jpg
