ozcanyardimci/IoT_gateway/reference-photos/2026-09-08-hardware-assembly-photos/photo_30_cf5ebd82.jpg

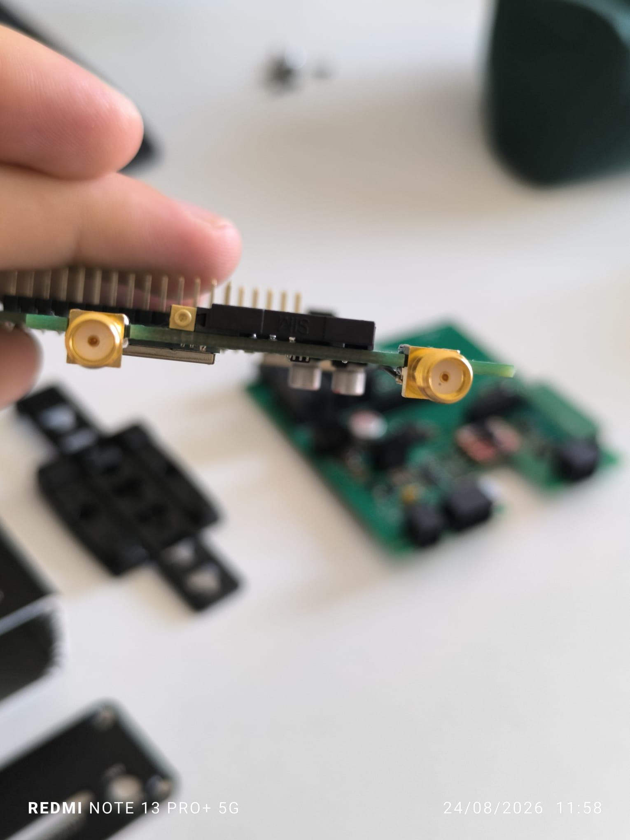
reference-photos/2026-09-08-hardware-assembly-photos/photo_30_cf5ebd82.jpg
