ozcanyardimci/IoT_gateway/reference-photos/2026-09-08-hardware-assembly-photos/photo_31_bf818aab.jpg

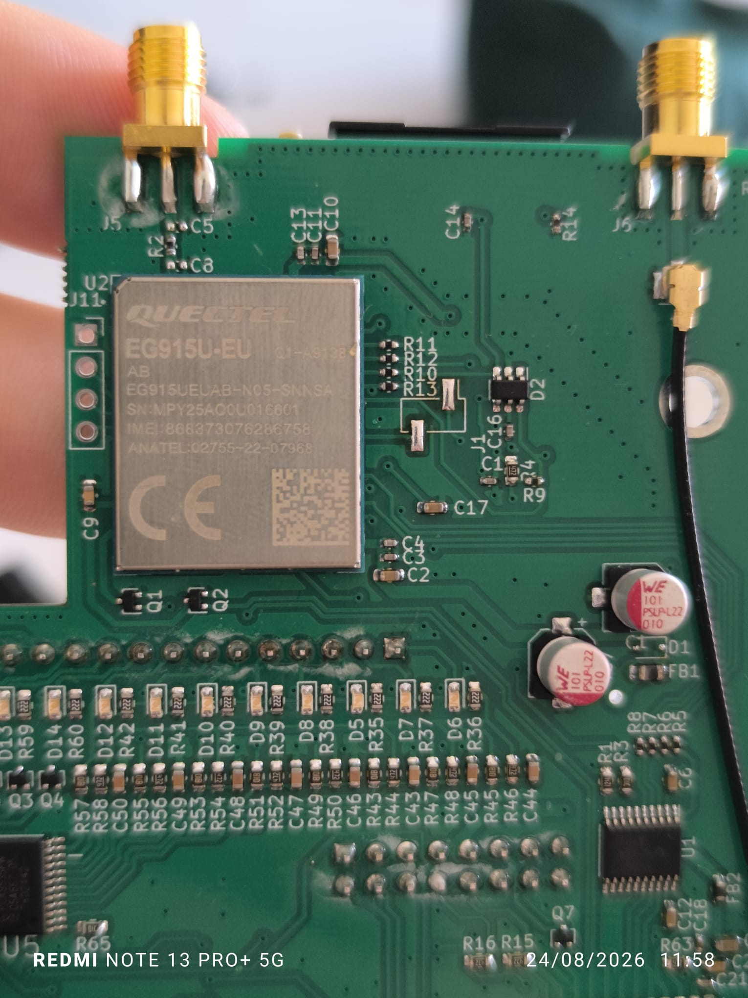
reference-photos/2026-09-08-hardware-assembly-photos/photo_31_bf818aab.jpg
