ozcanyardimci/IoT_gateway/reference-photos/2026-09-08-hardware-assembly-photos/photo_32_8d965cb2.jpg

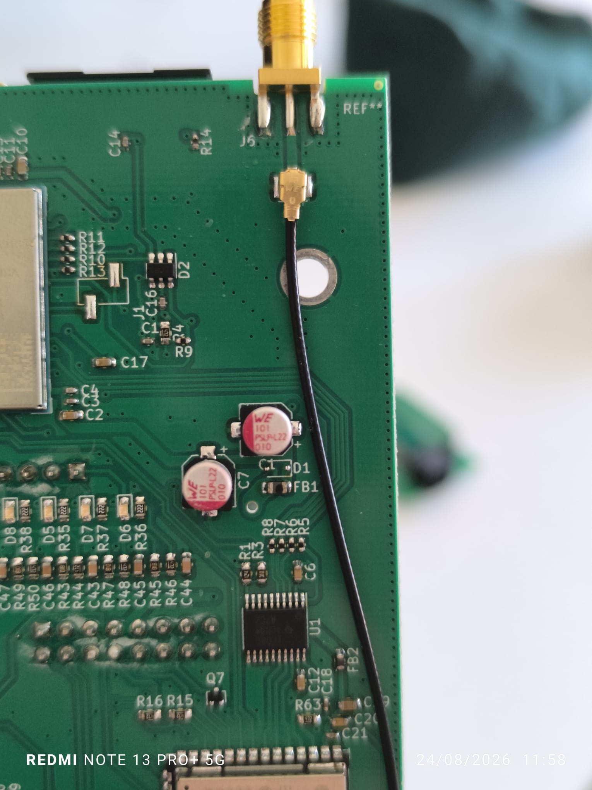
reference-photos/2026-09-08-hardware-assembly-photos/photo_32_8d965cb2.jpg
