ozcanyardimci/IoT_gateway/hardware/kicad/ioboard+lteboard/ioboard+lteboard/analog_io.kicad_sch

## KiCad design hardware/kicad/ioboard+lteboard/ioboard+lteboard/analog_io.kicad_sch (2026-09-25, an earlier design)

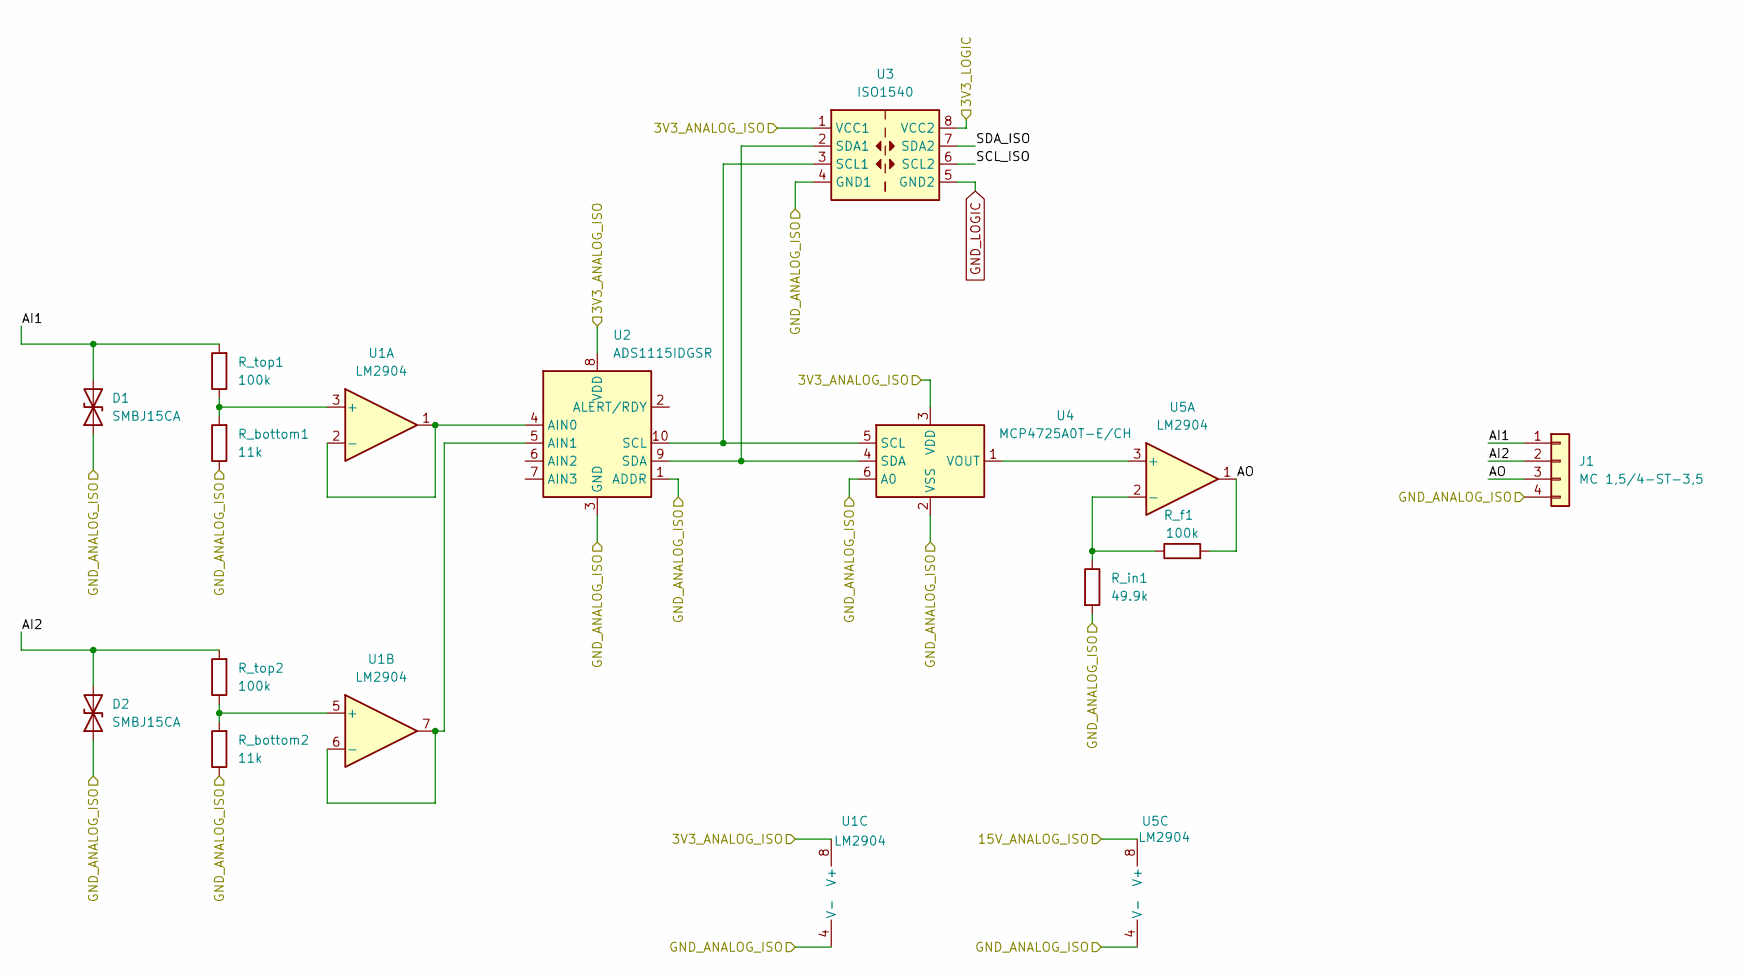
[picture p33: schematic analog_io.kicad_sch]

Parts:
D1, D2: SMBJ15CA
J1: MC 1,5/4-ST-3,5
R_bottom1, R_bottom2: 11k
R_f1: 100k
R_in1: 49.9k
R_top1, R_top2: 100k
U1, U5: LM2904
U2: ADS1115IDGSR; TSSOP-10_3x3mm_P0.5mm
U3: ISO1540; SOIC-8_3.9x4.9mm_P1.27mm
U4: MCP4725A0T-E/CH; SOT-23-6

Connections:
3V3_ANALOG_ISO: U1.8 (V+), U2.8 (VDD), U3.1 (VCC1), U4.3 (VDD)
3V3_LOGIC: U3.8 (VCC2)
15V_ANALOG_ISO: U5.8 (V+)
AI1: D1.2 (A2), J1.1, R_top1.2
AI2: D2.2 (A2), J1.2, R_top2.2
AO: J1.3, R_f1.2, U5.1
GND_ANALOG_ISO: D1.1 (A1), D2.1 (A1), J1.4, R_bottom1.1, R_bottom2.1, R_in1.2, U1.4 (V-), U2.1 (ADDR), U2.3 (GND), U3.4 (GND1), U4.2 (VSS), U4.6 (A0), U5.4 (V-)
GND_LOGIC: U3.5 (GND2)
unnamed: R_bottom1.2, R_top1.1, U1.3 (+)
unnamed: R_bottom2.2, R_top2.1, U1.5 (+)
unnamed: R_f1.1, R_in1.1, U5.2 (-)
unnamed: U1.1, U1.2 (-), U2.4 (AIN0)
unnamed: U1.6 (-), U1.7, U2.5 (AIN1)
unnamed: U2.9 (SDA), U3.2 (SDA1), U4.4 (SDA)
unnamed: U2.10 (SCL), U3.3 (SCL1), U4.5 (SCL)
unnamed: U4.1 (VOUT), U5.3 (+)
SCL_ISO: U3.6 (SCL2)
SDA_ISO: U3.7 (SDA2)
