ozcanyardimci/IoT_gateway/hardware/kicad/ioboard+lteboard/ioboard+lteboard/core-compute.kicad_sch

## KiCad design hardware/kicad/ioboard+lteboard/ioboard+lteboard/core-compute.kicad_sch (2026-09-25, an earlier design)

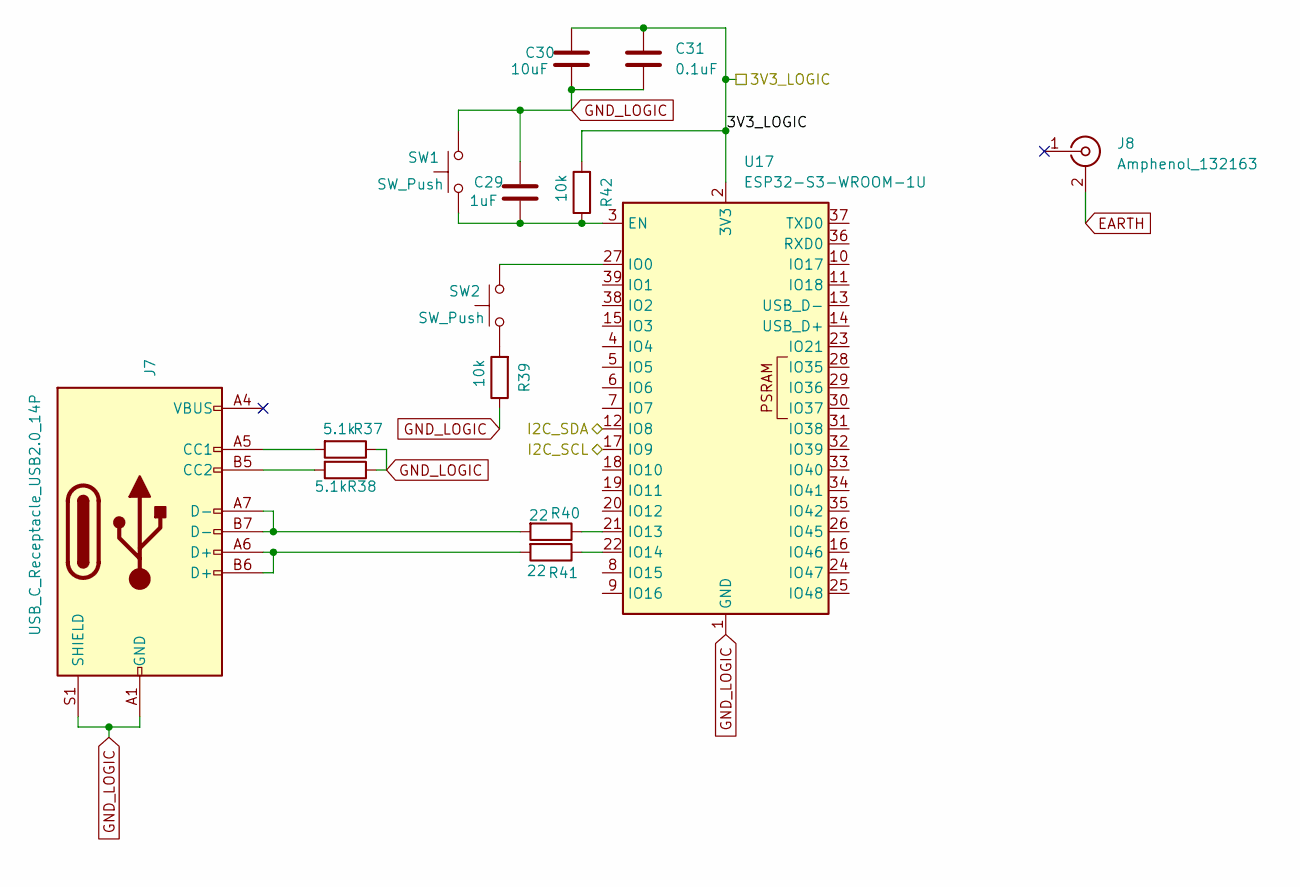
[picture p34: schematic core-compute.kicad_sch]

Parts:
C29: 1uF
C30: 10uF
C31: 0.1uF
J7: USB_C_Receptacle_USB2.0_14P
J8: Amphenol_132163
R37, R38: 5.1k
R39, R42: 10k
R40, R41: 22
SW1, SW2: SW_Push
U17: ESP32-S3-WROOM-1U

Connections:
3V3_LOGIC: C30.1, C31.1, R42.2, U17.2 (3V3)
EARTH: J8.2 (Ext)
GND_LOGIC: C29.1, C30.2, C31.2, J7.A1 (GND), J7.A12 (GND), J7.B1 (GND), J7.B12 (GND), J7.S1 (SHIELD), R37.1, R38.1, R39.1, SW1.2, U17.1 (GND), U17.40 (GND), U17.41 (GND)
I2C_SCL: U17.17 (IO9)
I2C_SDA: U17.12 (IO8)
unnamed: C29.2, R42.1, SW1.1, U17.3 (EN)
unnamed: J7.A4 (VBUS), J7.A9 (VBUS), J7.B4 (VBUS), J7.B9 (VBUS)
unnamed: J7.A5 (CC1), R37.2
unnamed: J7.A6 (D+), J7.B6 (D+), R41.2
unnamed: J7.A7 (D-), J7.B7 (D-), R40.2
unnamed: J7.B5 (CC2), R38.2
unnamed: R39.2, SW2.1
unnamed: R40.1, U17.21 (IO13)
unnamed: R41.1, U17.22 (IO14)
unnamed: SW2.2, U17.27 (IO0)
