ozcanyardimci/IoT_gateway/hardware/kicad/ioboard+lteboard/ioboard+lteboard/digital_inputs.kicad_sch

## KiCad design hardware/kicad/ioboard+lteboard/ioboard+lteboard/digital_inputs.kicad_sch (2026-09-25, an earlier design)

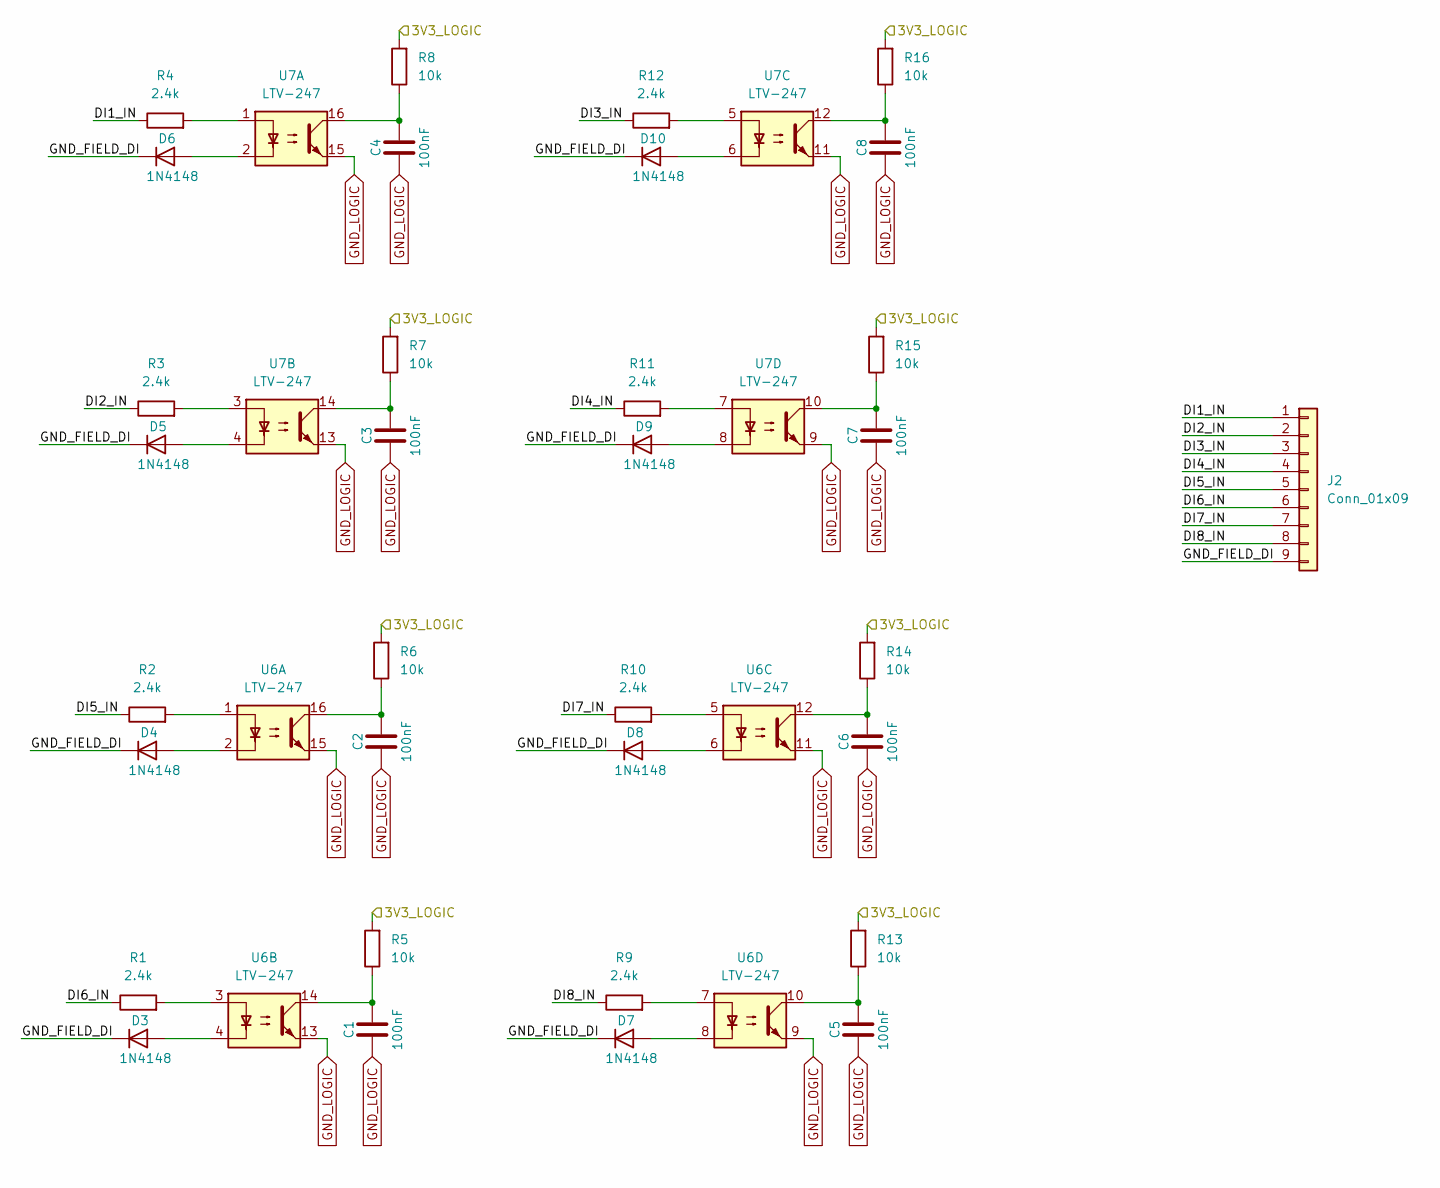
[picture p35: schematic digital_inputs.kicad_sch]

Parts:
C1, C2, C3, C4, C5, C6, C7, C8: 100nF
D3, D4, D5, D6, D7, D8, D9, D10: 1N4148
J2: Conn_01x09
R1, R2, R3, R4, R9, R10, R11, R12: 2.4k
R5, R6, R7, R8, R13, R14, R15, R16: 10k
U6, U7: LTV-247; SOP-16_4.4x10.4mm_P1.27mm

Connections:
3V3_LOGIC: R5.2, R6.2, R7.2, R8.2, R13.2, R14.2, R15.2, R16.2
DI1_IN: J2.1, R4.1
DI2_IN: J2.2, R3.1
DI3_IN: J2.3, R12.1
DI4_IN: J2.4, R11.1
DI5_IN: J2.5, R2.1
DI6_IN: J2.6, R1.1
DI7_IN: J2.7, R10.1
DI8_IN: J2.8, R9.1
GND_FIELD_DI: D3.1 (K), D4.1 (K), D5.1 (K), D6.1 (K), D7.1 (K), D8.1 (K), D9.1 (K), D10.1 (K), J2.9
GND_LOGIC: C1.1, C2.1, C3.1, C4.1, C5.1, C6.1, C7.1, C8.1, U6.9, U6.11, U6.13, U6.15, U7.9, U7.11, U7.13, U7.15
unnamed: C1.2, R5.1, U6.14
unnamed: C2.2, R6.1, U6.16
unnamed: C3.2, R7.1, U7.14
unnamed: C4.2, R8.1, U7.16
unnamed: C5.2, R13.1, U6.10
unnamed: C6.2, R14.1, U6.12
unnamed: C7.2, R15.1, U7.10
unnamed: C8.2, R16.1, U7.12
unnamed: D3.2 (A), U6.4
unnamed: D4.2 (A), U6.2
unnamed: D5.2 (A), U7.4
unnamed: D6.2 (A), U7.2
unnamed: D7.2 (A), U6.8
unnamed: D8.2 (A), U6.6
unnamed: D9.2 (A), U7.8
unnamed: D10.2 (A), U7.6
unnamed: R1.2, U6.3
unnamed: R2.2, U6.1
unnamed: R3.2, U7.3
unnamed: R4.2, U7.1
unnamed: R9.2, U6.7
unnamed: R10.2, U6.5
unnamed: R11.2, U7.7
unnamed: R12.2, U7.5
