ozcanyardimci/IoT_gateway/hardware/kicad/ioboard+lteboard/ioboard+lteboard/ethernet.kicad_sch

## KiCad design hardware/kicad/ioboard+lteboard/ioboard+lteboard/ethernet.kicad_sch (2026-09-25, an earlier design)

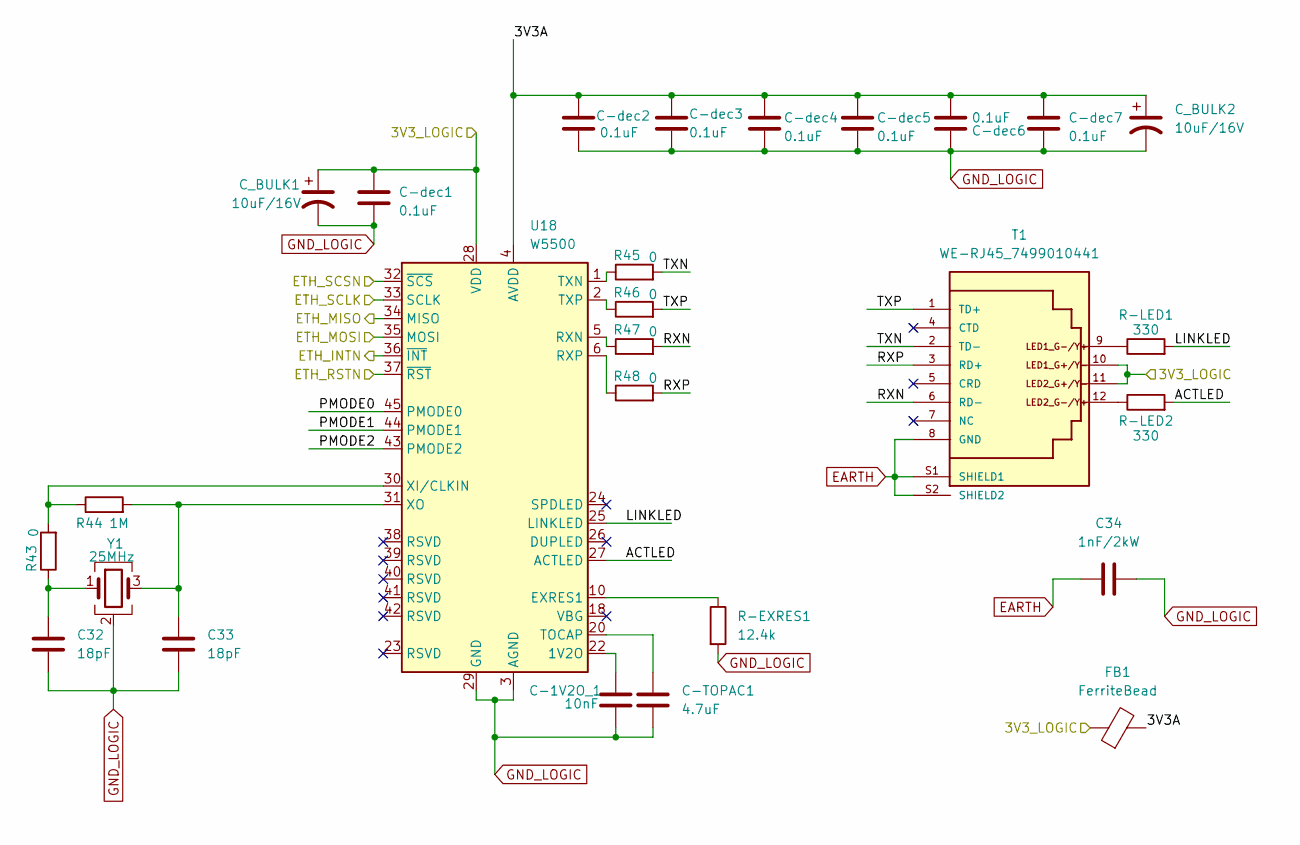
[picture p36: schematic ethernet.kicad_sch]

Parts:
C32, C33: 18pF
C34: 1nF/2kW
C-1V2O_1: 10nF
C-TOPAC1: 4.7uF
C-dec1, C-dec2, C-dec3, C-dec4, C-dec5, C-dec6, C-dec7: 0.1uF
C_BULK1, C_BULK2: 10uF/16V
FB1: FerriteBead
R43, R45, R46, R47, R48: 0
R44: 1M
R-EXRES1: 12.4k
R-LED1, R-LED2: 330
T1: WE-RJ45_7499010441; 7499010441
U18: W5500; LQFP-48_7x7mm_P0.5mm
Y1: 25MHz

Connections:
3V3A: C-dec2.1, C-dec3.1, C-dec4.1, C-dec5.1, C-dec6.1, C-dec7.1, C_BULK2.1, FB1.2, U18.4 (AVDD), U18.8 (AVDD), U18.11 (AVDD), U18.15 (AVDD), U18.17 (AVDD), U18.21 (AVDD)
3V3_LOGIC: C-dec1.1, C_BULK1.1, FB1.1, T1.10, T1.11, U18.28 (VDD)
ACTLED: R-LED2.2, U18.27 (ACTLED)
EARTH: C34.1, T1.8 (GND), T1.S1 (SHIELD1), T1.S2 (SHIELD2)
ETH_INTN: U18.36 (~INT)
ETH_MISO: U18.34 (MISO)
ETH_MOSI: U18.35 (MOSI)
ETH_RSTN: U18.37 (~RST)
ETH_SCLK: U18.33 (SCLK)
ETH_SCSN: U18.32 (~SCS)
GND_LOGIC: C32.2, C33.2, C34.2, C-1V2O_1.2, C-TOPAC1.2, C-dec1.2, C-dec2.2, C-dec3.2, C-dec4.2, C-dec5.2, C-dec6.2, C-dec7.2, C_BULK1.2, C_BULK2.2, R-EXRES1.2, U18.3 (AGND), U18.9 (AGND), U18.14 (AGND), U18.16 (AGND), U18.19 (AGND), U18.29 (GND), U18.48 (AGND), Y1.2 (G), Y1.4 (G)
LINKLED: R-LED1.2, U18.25 (LINKLED)
unnamed: C32.1, R43.1, Y1.1
unnamed: C33.1, R44.2, U18.31 (XO), Y1.3
unnamed: C-1V2O_1.1, U18.22 (1V2O)
unnamed: C-TOPAC1.1, U18.20 (TOCAP)
unnamed: R43.2, R44.1, U18.30 (XI/CLKIN)
unnamed: R45.1, U18.1 (TXN)
unnamed: R46.1, U18.2 (TXP)
unnamed: R47.1, U18.5 (RXN)
unnamed: R48.1, U18.6 (RXP)
unnamed: R-EXRES1.1, U18.10 (EXRES1)
unnamed: R-LED1.1, T1.9
unnamed: R-LED2.1, T1.12
PMODE0: U18.45 (PMODE0)
PMODE1: U18.44 (PMODE1)
PMODE2: U18.43 (PMODE2)
RXN: R47.2, T1.6 (RD-)
RXP: R48.2, T1.3 (RD+)
TXN: R45.2, T1.2 (TD-)
TXP: R46.2, T1.1 (TD+)
