ozcanyardimci/IoT_gateway/hardware/kicad/ioboard+lteboard/ioboard+lteboard/lte.kicad_sch

## KiCad design hardware/kicad/ioboard+lteboard/ioboard+lteboard/lte.kicad_sch (2026-09-25, an earlier design)

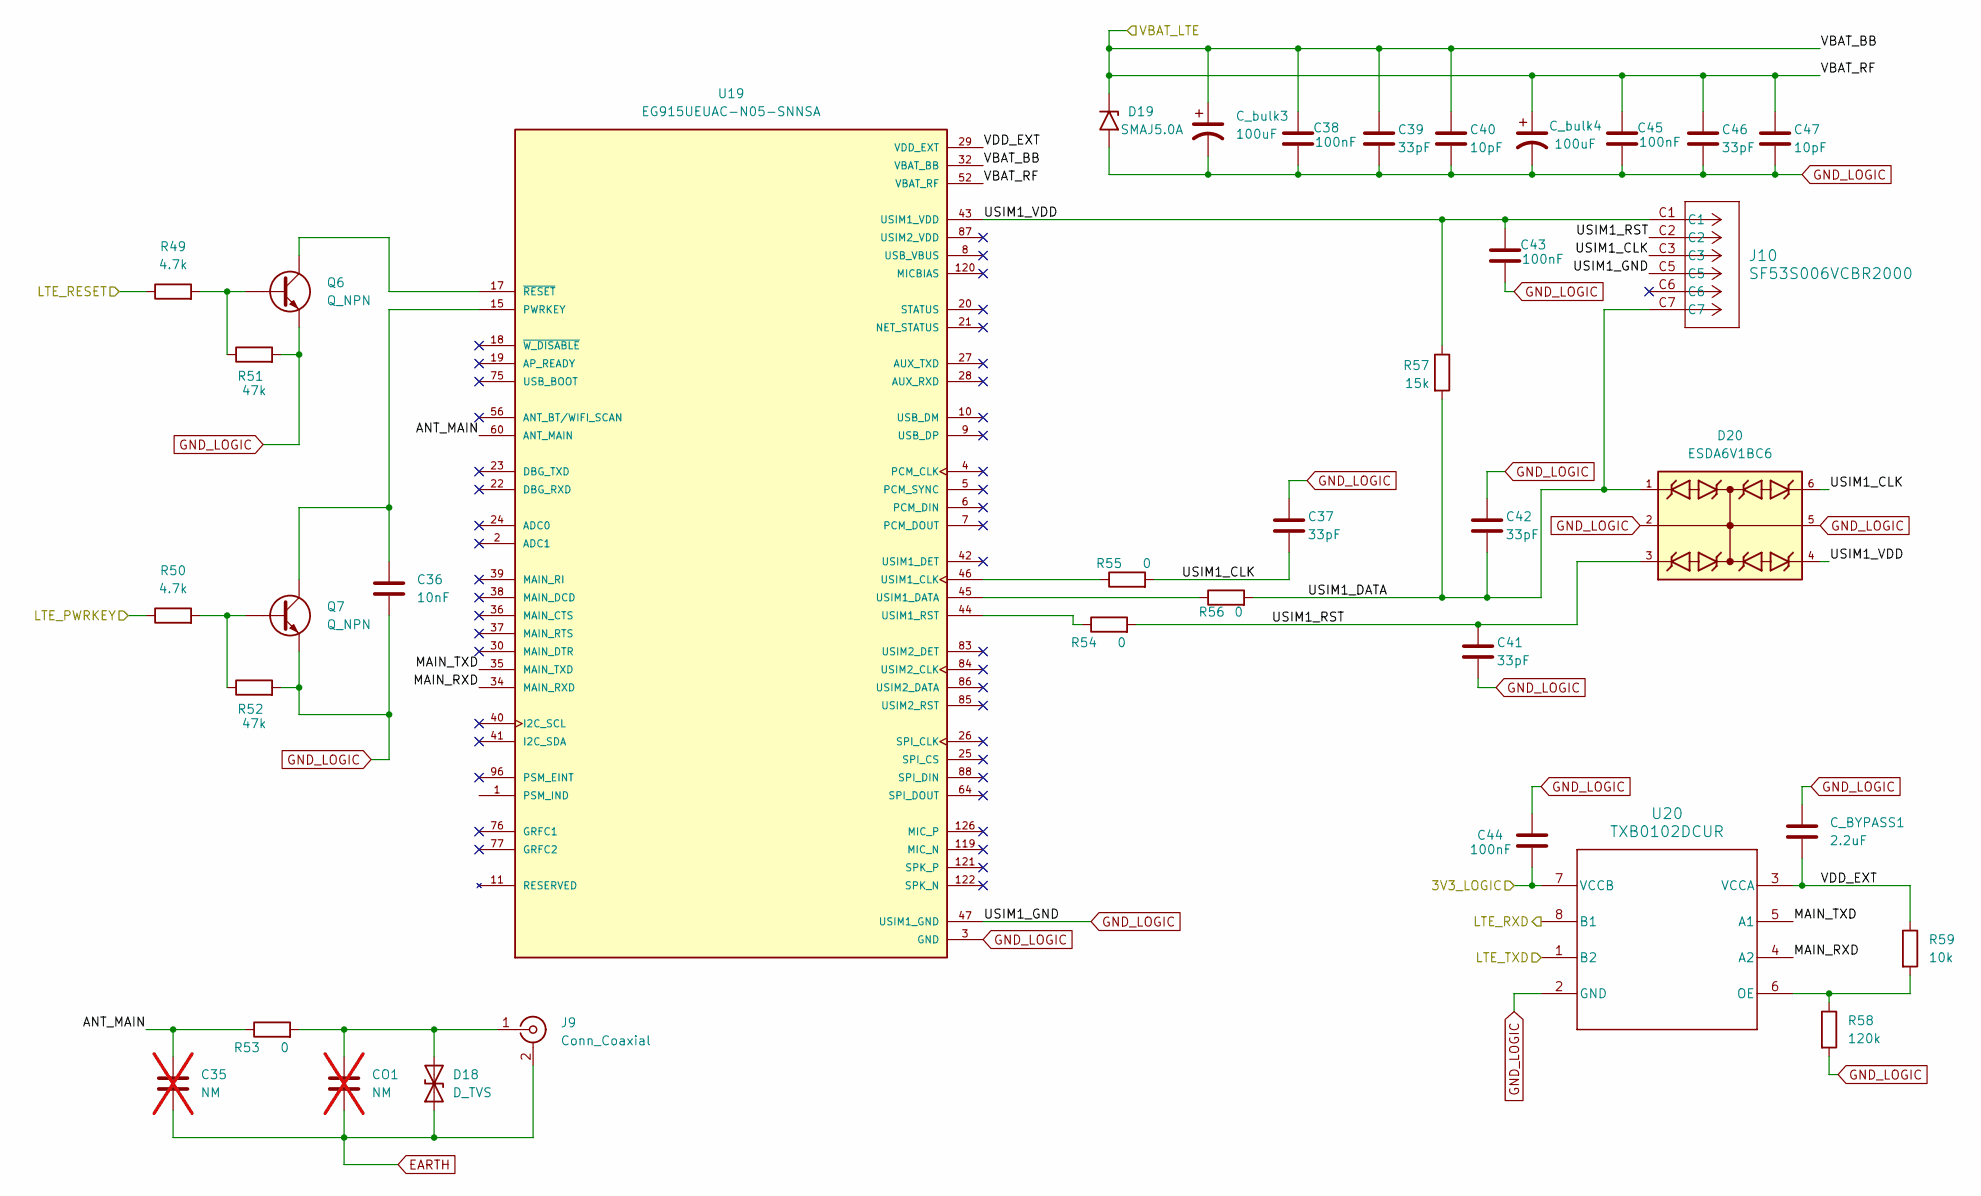
[picture p37: schematic lte.kicad_sch]

Parts:
C35: NM; not fitted
C36: 10nF
C37, C39, C41, C42, C46: 33pF
C38, C43, C44, C45: 100nF
C40, C47: 10pF
CO1: NM; not fitted
C_BYPASS1: 2.2uF
C_bulk3, C_bulk4: 100uF
D18: D_TVS
D19: SMAJ5.0A; D_SMA
D20: ESDA6V1BC6; SOT95P280X145-6N; PARTREV 2
J9: Conn_Coaxial
J10: SF53S006VCBR2000; CONN_SF53S006VCBR2000_JAE
Q6, Q7: Q_NPN
R49, R50: 4.7k
R51, R52: 47k
R53, R54, R55, R56: 0
R57: 15k
R58: 120k
R59: 10k
U19: EG915UEUAC-N05-SNNSA; XCVR_EG915UEUAC-N05-SNNSA
U20: TXB0102DCUR; DCU0008A_N

Connections:
3V3_LOGIC: C44.2, U20.7 (VCCB)
ANT_MAIN: C35.1, R53.1, U19.60 (ANT_MAIN)
EARTH: C35.2, CO1.2, D18.1 (A1), J9.2 (Ext)
GND_LOGIC: C36.2, C37.1, C38.2, C39.2, C40.2, C41.2, C42.1, C43.2, C44.1, C45.2, C46.2, C47.2, C_BYPASS1.1, C_bulk3.2, C_bulk4.2, D19.2 (A2), D20.2, D20.5, J10.C5, Q6.E, Q7.E, R51.2, R52.2, R58.2, U19.3 (GND), U19.31 (GND), U19.47 (USIM1_GND), U19.48 (GND), U19.50 (GND), U19.54 (GND), U19.55 (GND), U19.58 (GND), U19.59 (GND), U19.61 (GND), U19.62 (GND), U19.67 (GND), U19.68 (GND), U19.69 (GND), U19.70 (GND), U19.71 (GND), U19.72 (GND), U19.73 (GND), U19.74 (GND), U19.79 (GND), U19.80 (GND), U19.81 (GND), U19.82 (GND), U19.89 (GND), U19.90 (GND), U19.91 (GND), U19.100 (GND), U19.101 (GND), U19.102 (GND), U20.2 (GND)
LTE_PWRKEY: R50.1
LTE_RESET: R49.1
LTE_RXD: U20.8 (B1)
LTE_TXD: U20.1 (B2)
MAIN_RXD: U19.34 (MAIN_RXD), U20.4 (A2)
MAIN_TXD: U19.35 (MAIN_TXD), U20.5 (A1)
unnamed: C36.1, Q7.C, U19.15 (PWRKEY)
unnamed: CO1.1, D18.2 (A2), J9.1 (In), R53.2
unnamed: Q6.B, R49.2, R51.1
unnamed: Q6.C, U19.17 (~RESET)
unnamed: Q7.B, R50.2, R52.1
unnamed: R54.1, U19.44 (USIM1_RST)
unnamed: R55.1, U19.46 (USIM1_CLK)
unnamed: R56.1, U19.45 (USIM1_DATA)
unnamed: R58.1, R59.2, U20.6 (OE)
unnamed: U19.11 (RESERVED), U19.12 (RESERVED), U19.13 (RESERVED), U19.14 (RESERVED), U19.16 (RESERVED), U19.49 (RESERVED), U19.51 (RESERVED), U19.57 (RESERVED), U19.63 (RESERVED), U19.65 (RESERVED), U19.66 (RESERVED), U19.78 (RESERVED), U19.92 (RESERVED), U19.93 (RESERVED), U19.94 (RESERVED), U19.95 (RESERVED), U19.97 (RESERVED), U19.98 (RESERVED), U19.99 (RESERVED), U19.103 (RESERVED), U19.104 (RESERVED), U19.105 (RESERVED), U19.106 (RESERVED), U19.107 (RESERVED), U19.108 (RESERVED), U19.109 (RESERVED), U19.110 (RESERVED), U19.111 (RESERVED), U19.112 (RESERVED), U19.113 (RESERVED), U19.114 (RESERVED), U19.115 (RESERVED), U19.116 (RESERVED), U19.117 (RESERVED), U19.118 (RESERVED), U19.123 (RESERVED), U19.124 (RESERVED), U19.125 (RESERVED)
USIM1_CLK: C37.2, D20.6, J10.C3, R55.2
USIM1_DATA: C42.2, D20.1, J10.C7, R56.2, R57.2
USIM1_RST: C41.1, D20.3, J10.C2, R54.2
USIM1_VDD: C43.1, D20.4, J10.C1, R57.1, U19.43 (USIM1_VDD)
VBAT_BB: C38.1, C39.1, C40.1, C45.1, C46.1, C47.1, C_bulk3.1, C_bulk4.1, D19.1 (A1), U19.32 (VBAT_BB), U19.33 (VBAT_BB), U19.52 (VBAT_RF), U19.53 (VBAT_RF)
VDD_EXT: C_BYPASS1.2, R59.1, U19.29 (VDD_EXT), U20.3 (VCCA)
