ozcanyardimci/IoT_gateway/hardware/kicad/ioboard+lteboard/ioboard+lteboard/power.kicad_sch

## KiCad design hardware/kicad/ioboard+lteboard/ioboard+lteboard/power.kicad_sch (2026-09-25, an earlier design)

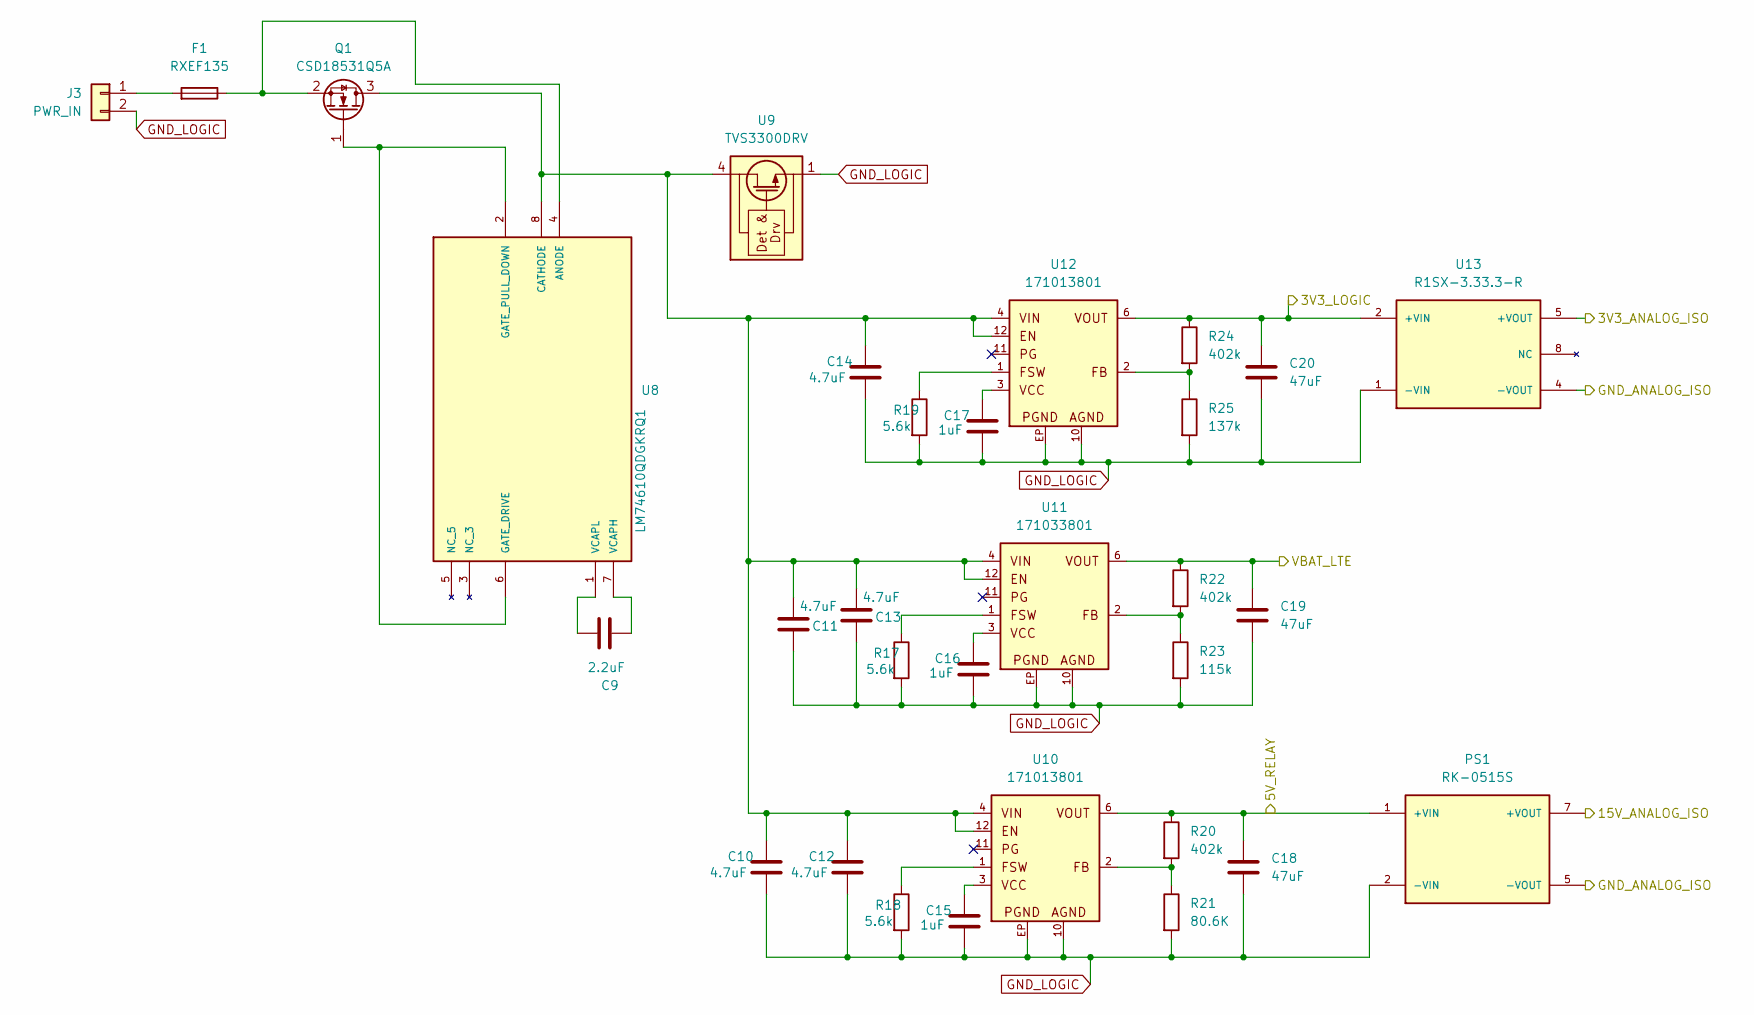
[picture p38: schematic power.kicad_sch]

Parts:
C9: 2.2uF
C10, C11, C12, C13, C14: 4.7uF
C15, C16, C17: 1uF
C18, C19, C20: 47uF
F1: RXEF135
J3: PWR_IN; MPN 1840366
PS1: RK-0515S; CONV_RK-0515S; PARTREV 4
Q1: CSD18531Q5A
R17, R18, R19: 5.6k
R20, R22, R24: 402k
R21: 80.6K
R23: 115k
R25: 137k
U8: LM74610QDGKRQ1; SOP65P490X110-8N; PARTREV B
U9: TVS3300DRV; WSON-6-1EP_2x2mm_P0.65mm_EP1x1.6mm
U10, U12: 171013801; WPME-VDLM_LGA-12EP
U11: 171033801; WPME-VDLM_LGA-12EP
U13: R1SX-3.33.3-R; CONV_R1SX-3.33.3-R; PARTREV 5

Connections:
3V3_ANALOG_ISO: U13.5 (+VOUT)
3V3_LOGIC: C20.1, R24.1, U12.6, U12.7, U13.2 (+VIN)
5V_RELAY: C18.1, PS1.1 (+VIN), R20.1, U10.6, U10.7
15V_ANALOG_ISO: PS1.7 (+VOUT)
GND_ANALOG_ISO: PS1.5 (-VOUT), U13.4 (-VOUT)
GND_LOGIC: C10.2, C11.2, C12.2, C13.2, C14.2, C15.2, C16.2, C17.2, C18.2, C19.2, C20.2, J3.2, PS1.2 (-VIN), R17.2, R18.2, R19.2, R21.2, R23.2, R25.2, U9.1 (GND), U9.2 (GND), U9.3 (GND), U9.7 (GND), U10.10, U10.EP, U11.10, U11.EP, U12.10, U12.EP, U13.1 (-VIN)
unnamed: C9.1, U8.7 (VCAPH)
unnamed: C9.2, U8.1 (VCAPL)
unnamed: C10.1, C11.1, C12.1, C13.1, C14.1, Q1.3 (D), U8.8 (CATHODE), U9.4 (IN), U9.5 (IN), U9.6 (IN), U10.4, U10.5, U10.9, U10.12, U11.4, U11.5, U11.9, U11.12, U12.4, U12.5, U12.9, U12.12
unnamed: C15.1, U10.3
unnamed: C16.1, U11.3
unnamed: C17.1, U12.3
unnamed: F1.1, Q1.2 (S), U8.4 (ANODE)
unnamed: F1.2, J3.1
unnamed: Q1.1 (G), U8.2 (GATE_PULL_DOWN), U8.6 (GATE_DRIVE)
unnamed: R17.1, U11.1
unnamed: R18.1, U10.1
unnamed: R19.1, U12.1
unnamed: R20.2, R21.1, U10.2
unnamed: R22.2, R23.1, U11.2
unnamed: R24.2, R25.1, U12.2
VBAT_LTE: C19.1, R22.1, U11.6, U11.7
