ozcanyardimci/IoT_gateway/hardware/kicad/ioboard+lteboard/ioboard+lteboard/relay_outputs.kicad_sch

## KiCad design hardware/kicad/ioboard+lteboard/ioboard+lteboard/relay_outputs.kicad_sch (2026-09-25, an earlier design)

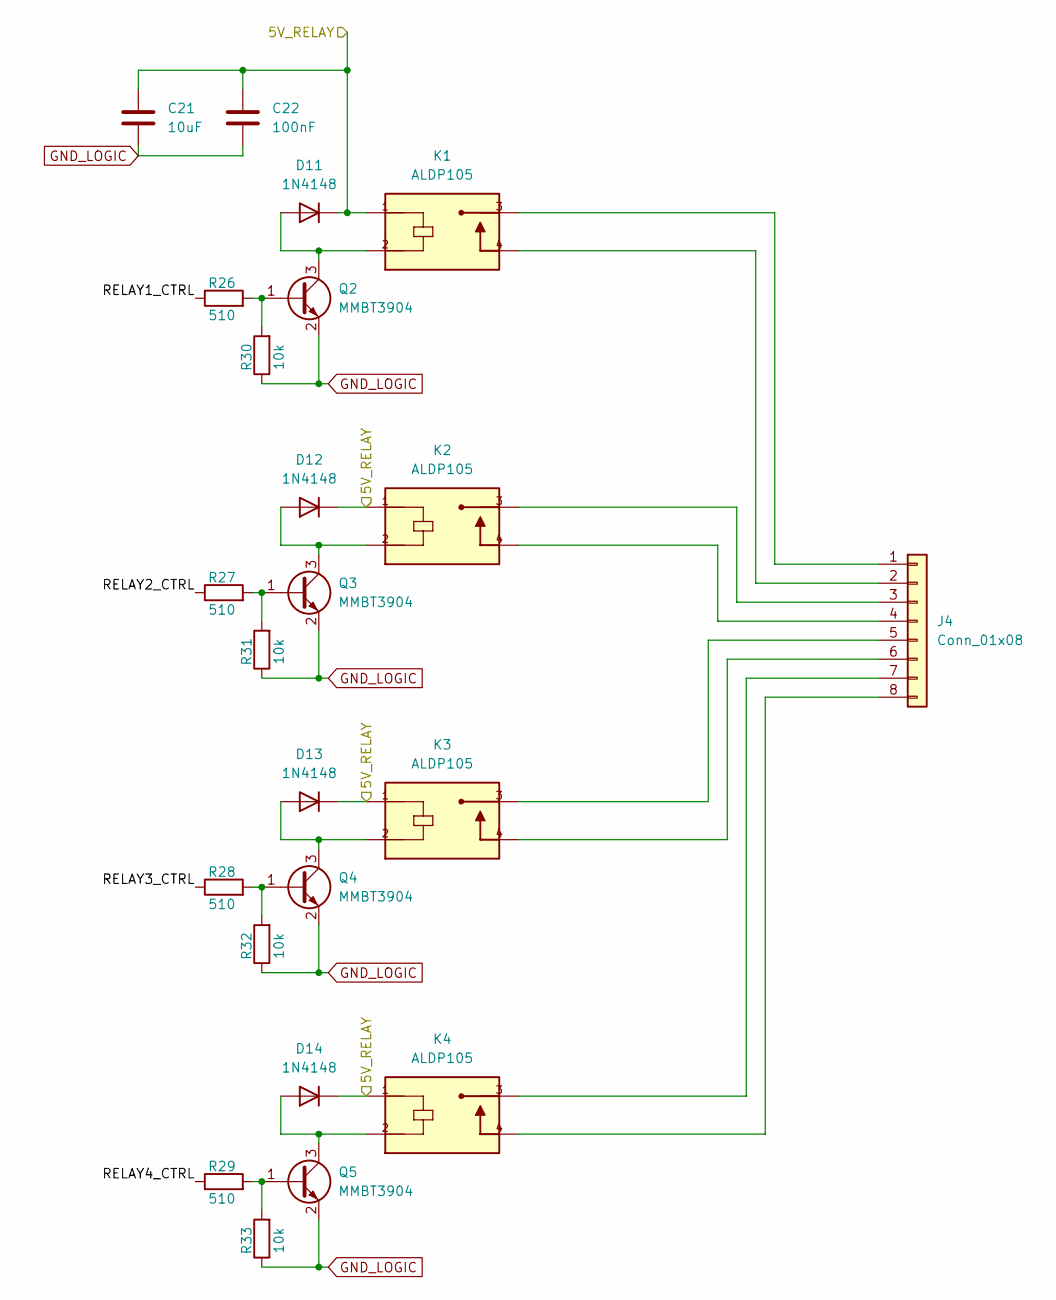
[picture p39: schematic relay_outputs.kicad_sch]

Parts:
C21: 10uF
C22: 100nF
D11, D12, D13, D14: 1N4148
J4: Conn_01x08
K1, K2, K3, K4: ALDP105; RELAY_ALDP105; PARTREV 2024.10
Q2, Q3, Q4, Q5: MMBT3904; SOT-23
R26, R27, R28, R29: 510
R30, R31, R32, R33: 10k

Connections:
5V_RELAY: C21.1, C22.1, D11.1 (K), D12.1 (K), D13.1 (K), D14.1 (K), K1.1, K2.1, K3.1, K4.1
GND_LOGIC: C21.2, C22.2, Q2.2 (E), Q3.2 (E), Q4.2 (E), Q5.2 (E), R30.1, R31.1, R32.1, R33.1
unnamed: D11.2 (A), K1.2, Q2.3 (C)
unnamed: D12.2 (A), K2.2, Q3.3 (C)
unnamed: D13.2 (A), K3.2, Q4.3 (C)
unnamed: D14.2 (A), K4.2, Q5.3 (C)
unnamed: J4.1, K1.3
unnamed: J4.2, K1.4
unnamed: J4.3, K2.3
unnamed: J4.4, K2.4
unnamed: J4.5, K3.3
unnamed: J4.6, K3.4
unnamed: J4.7, K4.3
unnamed: J4.8, K4.4
unnamed: Q2.1 (B), R26.2, R30.2
unnamed: Q3.1 (B), R27.2, R31.2
unnamed: Q4.1 (B), R28.2, R32.2
unnamed: Q5.1 (B), R29.2, R33.2
RELAY1_CTRL: R26.1
RELAY2_CTRL: R27.1
RELAY3_CTRL: R28.1
RELAY4_CTRL: R29.1
