ozcanyardimci/IoT_gateway/hardware/kicad/ioboard+lteboard/ioboard+lteboard/rs232.kicad_sch

## KiCad design hardware/kicad/ioboard+lteboard/ioboard+lteboard/rs232.kicad_sch (2026-09-19)

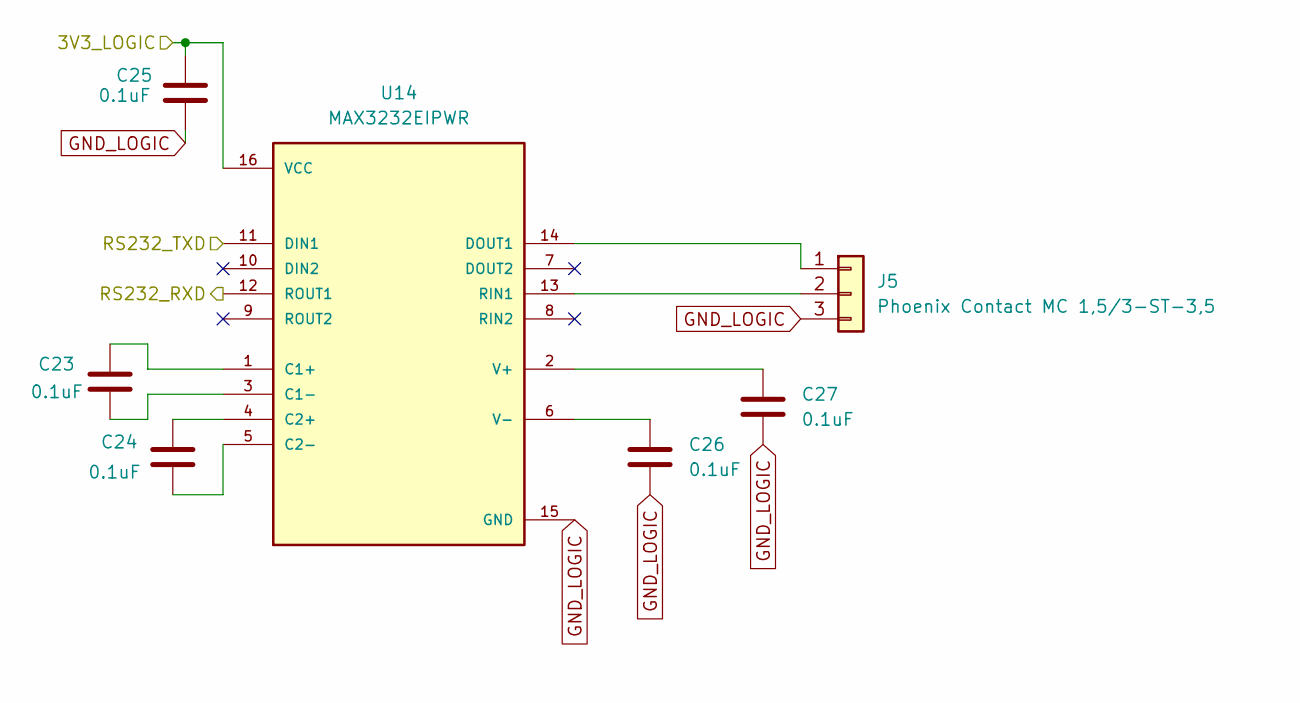
[picture p40: schematic rs232.kicad_sch]

Parts:
C23, C24, C25, C26, C27: 0.1uF
J5: Phoenix Contact MC 1,5/3-ST-3,5
U14: MAX3232EIPWR; SOP65P640X120-16N; PARTREV D

Connections:
3V3_LOGIC: C25.1, U14.16 (VCC)
GND_LOGIC: C25.2, C26.2, C27.2, J5.3, U14.15 (GND)
unnamed: C23.1, U14.1 (C1+)
unnamed: C23.2, U14.3 (C1-)
unnamed: C24.1, U14.4 (C2+)
unnamed: C24.2, U14.5 (C2-)
unnamed: C26.1, U14.6 (V-)
unnamed: C27.1, U14.2 (V+)
unnamed: J5.1, U14.14 (DOUT1)
unnamed: J5.2, U14.13 (RIN1)
RS232_RXD: U14.12 (ROUT1)
RS232_TXD: U14.11 (DIN1)
