ozcanyardimci/IoT_gateway/hardware/kicad/ioboard+lteboard/ioboard+lteboard/rs485.kicad_sch

## KiCad design hardware/kicad/ioboard+lteboard/ioboard+lteboard/rs485.kicad_sch (2026-09-25, an earlier design)

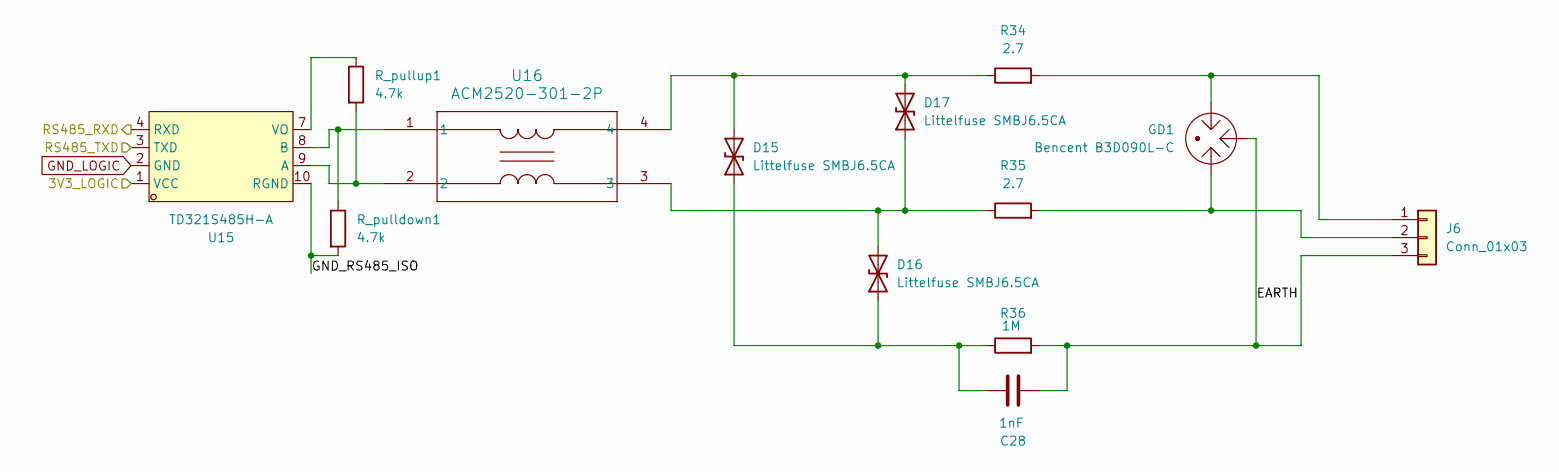
[picture p41: schematic rs485.kicad_sch]

Parts:
C28: 1nF
D15, D16, D17: Littelfuse SMBJ6.5CA
GD1: Bencent B3D090L-C
J6: Conn_01x03
R34, R35: 2.7
R36: 1M
R_pulldown1: 4.7k
R_pullup1: 4.7k
U15: TD321S485H-A; COMM-SMD_TD321S485H-A; MPN TD321S485H-A; LCSC Part C190643
U16: ACM2520-301-2P; ACM2520-2P_TDK

Connections:
3V3_LOGIC: U15.1 (VCC)
EARTH: C28.2, GD1.2, J6.3, R36.2
GND_LOGIC: U15.2 (GND)
GND_RS485_ISO: R_pulldown1.2, U15.10 (RGND)
unnamed: C28.1, D15.1 (A1), D16.1 (A1), R36.1
unnamed: D15.2 (A2), D17.2 (A2), R34.1, U16.4
unnamed: D16.2 (A2), D17.1 (A1), R35.1, U16.3
unnamed: GD1.1, J6.2, R35.2
unnamed: GD1.3, J6.1, R34.2
unnamed: R_pulldown1.1, U15.8 (B), U16.1
unnamed: R_pullup1.1, U15.7 (VO)
unnamed: R_pullup1.2, U15.9 (A), U16.2
RS485_RXD: U15.4 (RXD)
RS485_TXD: U15.3 (TXD)
