ozcanyardimci/IoT_gateway/hardware/kicad/ioboard+lteboard/ioboard+lteboard/status_indication.kicad_sch

## KiCad design hardware/kicad/ioboard+lteboard/ioboard+lteboard/status_indication.kicad_sch (2026-09-19)

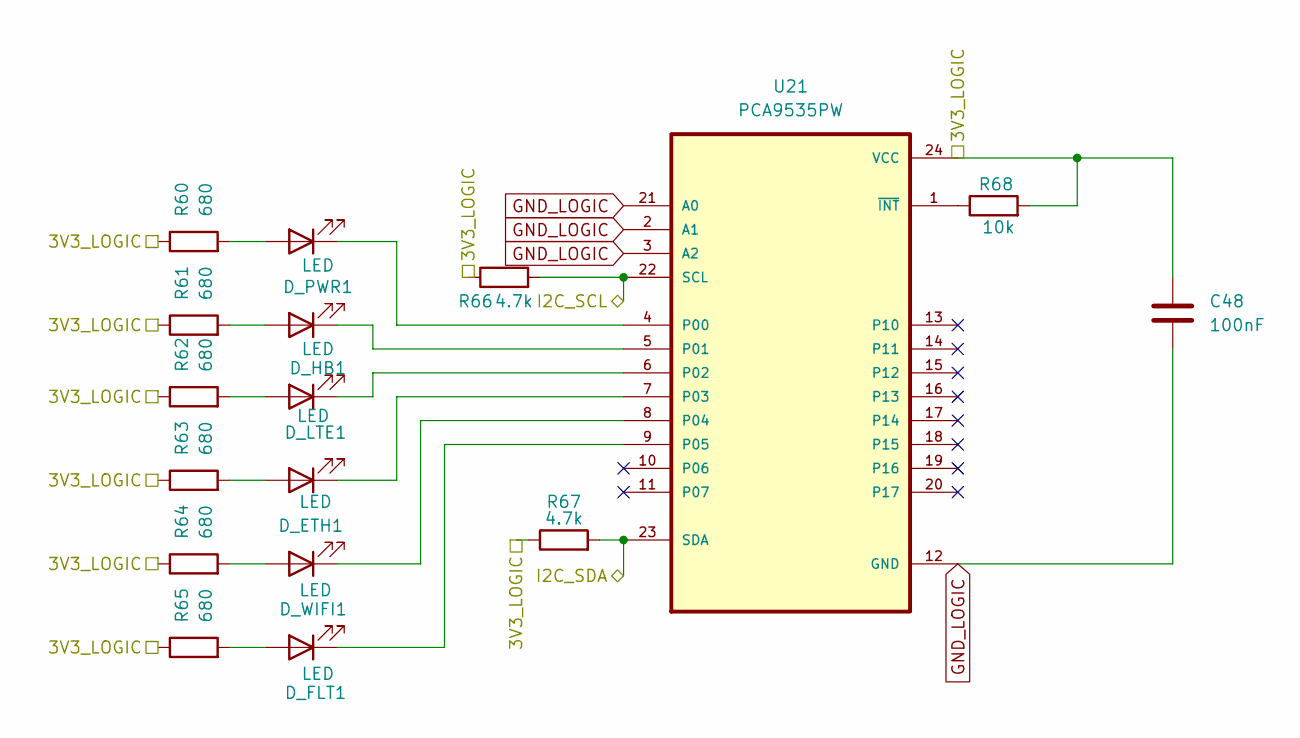
[picture p42: schematic status_indication.kicad_sch]

Parts:
C48: 100nF
D_ETH1: LED
D_FLT1: LED
D_HB1: LED
D_LTE1: LED
D_PWR1: LED
D_WIFI1: LED
R60, R61, R62, R63, R64, R65: 680
R66, R67: 4.7k
R68: 10k
U21: PCA9535PW; SOP65P640X120-24N

Connections:
3V3_LOGIC: C48.1, R60.1, R61.1, R62.1, R63.1, R64.1, R65.1, R66.1, R67.1, R68.2, U21.24 (VCC)
GND_LOGIC: C48.2, U21.2 (A1), U21.3 (A2), U21.12 (GND), U21.21 (A0)
I2C_SCL: R66.2, U21.22 (SCL)
I2C_SDA: R67.2, U21.23 (SDA)
unnamed: D_ETH1.1 (K), U21.7 (P03)
unnamed: D_ETH1.2 (A), R63.2
unnamed: D_FLT1.1 (K), U21.9 (P05)
unnamed: D_FLT1.2 (A), R65.2
unnamed: D_HB1.1 (K), U21.5 (P01)
unnamed: D_HB1.2 (A), R61.2
unnamed: D_LTE1.1 (K), U21.6 (P02)
unnamed: D_LTE1.2 (A), R62.2
unnamed: D_PWR1.1 (K), U21.4 (P00)
unnamed: D_PWR1.2 (A), R60.2
unnamed: D_WIFI1.1 (K), U21.8 (P04)
unnamed: D_WIFI1.2 (A), R64.2
unnamed: R68.1, U21.1 (~INT)
