ozcanyardimci/IoT_gateway/hardware/kicad/lteboard/lteboard/core-compute.kicad_sch

## KiCad design hardware/kicad/lteboard/lteboard/core-compute.kicad_sch (2026-09-13)

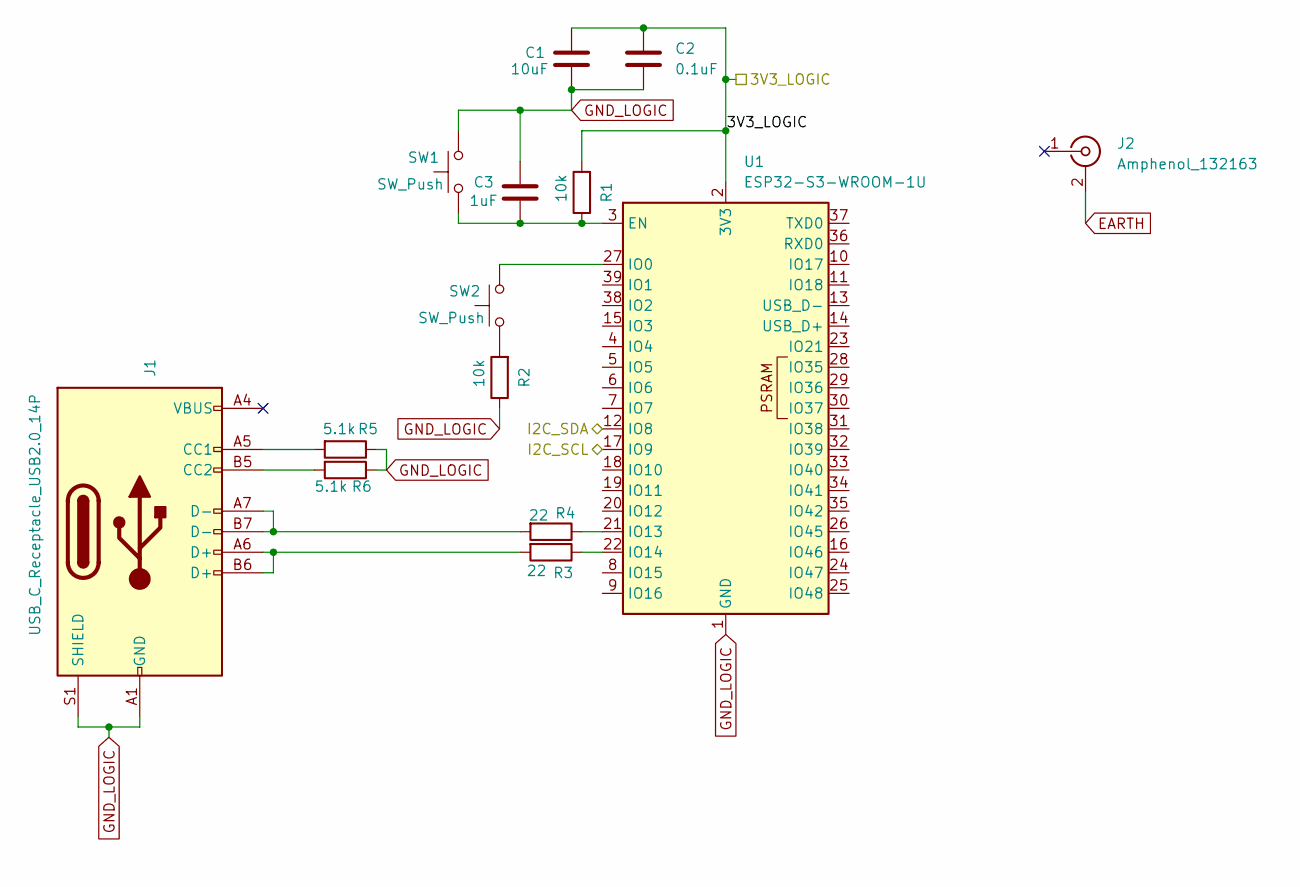
[picture p43: schematic core-compute.kicad_sch]

Parts:
C1: 10uF
C2: 0.1uF
C3: 1uF
J1: USB_C_Receptacle_USB2.0_14P
J2: Amphenol_132163
R1, R2: 10k
R3, R4: 22
R5, R6: 5.1k
SW1, SW2: SW_Push
U1: ESP32-S3-WROOM-1U

Connections:
3V3_LOGIC: C1.1, C2.1, R1.2, U1.2 (3V3)
EARTH: J2.2 (Ext)
GND_LOGIC: C1.2, C2.2, C3.1, J1.A1 (GND), J1.A12 (GND), J1.B1 (GND), J1.B12 (GND), J1.S1 (SHIELD), R2.1, R5.1, R6.1, SW1.2, U1.1 (GND), U1.40 (GND), U1.41 (GND)
I2C_SCL: U1.17 (IO9)
I2C_SDA: U1.12 (IO8)
unnamed: C3.2, R1.1, SW1.1, U1.3 (EN)
unnamed: J1.A4 (VBUS), J1.A9 (VBUS), J1.B4 (VBUS), J1.B9 (VBUS)
unnamed: J1.A5 (CC1), R5.2
unnamed: J1.A6 (D+), J1.B6 (D+), R3.2
unnamed: J1.A7 (D-), J1.B7 (D-), R4.2
unnamed: J1.B5 (CC2), R6.2
unnamed: R2.2, SW2.1
unnamed: R3.1, U1.22 (IO14)
unnamed: R4.1, U1.21 (IO13)
unnamed: SW2.2, U1.27 (IO0)
