ozcanyardimci/IoT_gateway/hardware/kicad/lteboard/lteboard/ethernet.kicad_sch

## KiCad design hardware/kicad/lteboard/lteboard/ethernet.kicad_sch (2026-09-13)

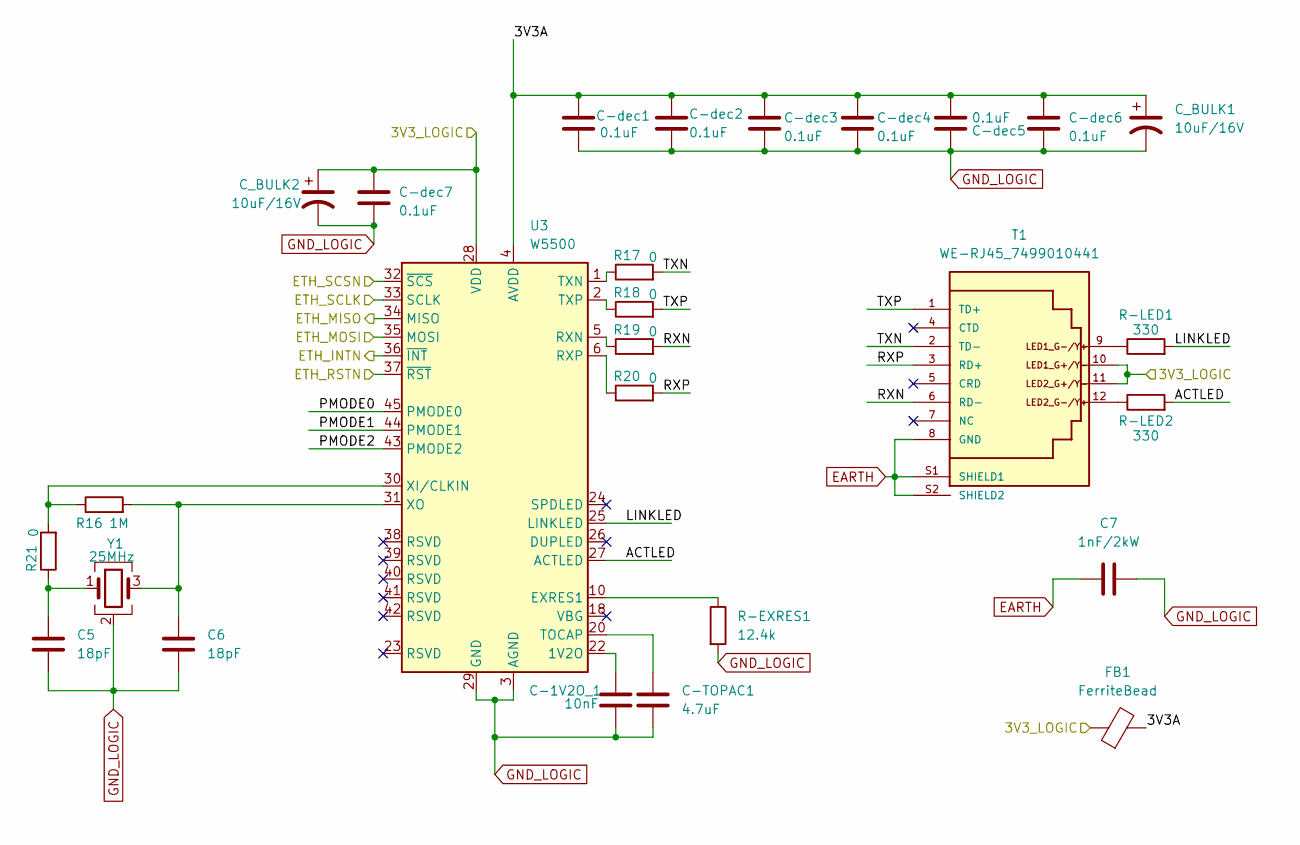
[picture p44: schematic ethernet.kicad_sch]

Parts:
C5, C6: 18pF
C7: 1nF/2kW
C-1V2O_1: 10nF
C-TOPAC1: 4.7uF
C-dec1, C-dec2, C-dec3, C-dec4, C-dec5, C-dec6, C-dec7: 0.1uF
C_BULK1, C_BULK2: 10uF/16V
FB1: FerriteBead
R16: 1M
R17, R18, R19, R20, R21: 0
R-EXRES1: 12.4k
R-LED1, R-LED2: 330
T1: WE-RJ45_7499010441; 7499010441
U3: W5500; LQFP-48_7x7mm_P0.5mm
Y1: 25MHz

Connections:
3V3A: C-dec1.1, C-dec2.1, C-dec3.1, C-dec4.1, C-dec5.1, C-dec6.1, C_BULK1.1, FB1.2, U3.4 (AVDD), U3.8 (AVDD), U3.11 (AVDD), U3.15 (AVDD), U3.17 (AVDD), U3.21 (AVDD)
3V3_LOGIC: C-dec7.1, C_BULK2.1, FB1.1, T1.10, T1.11, U3.28 (VDD)
ACTLED: R-LED2.2, U3.27 (ACTLED)
EARTH: C7.1, T1.8 (GND), T1.S1 (SHIELD1), T1.S2 (SHIELD2)
ETH_INTN: U3.36 (~INT)
ETH_MISO: U3.34 (MISO)
ETH_MOSI: U3.35 (MOSI)
ETH_RSTN: U3.37 (~RST)
ETH_SCLK: U3.33 (SCLK)
ETH_SCSN: U3.32 (~SCS)
GND_LOGIC: C5.2, C6.2, C7.2, C-1V2O_1.2, C-TOPAC1.2, C-dec1.2, C-dec2.2, C-dec3.2, C-dec4.2, C-dec5.2, C-dec6.2, C-dec7.2, C_BULK1.2, C_BULK2.2, R-EXRES1.2, U3.3 (AGND), U3.9 (AGND), U3.14 (AGND), U3.16 (AGND), U3.19 (AGND), U3.29 (GND), U3.48 (AGND), Y1.2 (G), Y1.4 (G)
LINKLED: R-LED1.2, U3.25 (LINKLED)
unnamed: C5.1, R21.1, Y1.1
unnamed: C6.1, R16.2, U3.31 (XO), Y1.3
unnamed: C-1V2O_1.1, U3.22 (1V2O)
unnamed: C-TOPAC1.1, U3.20 (TOCAP)
unnamed: R16.1, R21.2, U3.30 (XI/CLKIN)
unnamed: R17.1, U3.1 (TXN)
unnamed: R18.1, U3.2 (TXP)
unnamed: R19.1, U3.5 (RXN)
unnamed: R20.1, U3.6 (RXP)
unnamed: R-EXRES1.1, U3.10 (EXRES1)
unnamed: R-LED1.1, T1.9
unnamed: R-LED2.1, T1.12
PMODE0: U3.45 (PMODE0)
PMODE1: U3.44 (PMODE1)
PMODE2: U3.43 (PMODE2)
RXN: R19.2, T1.6 (RD-)
RXP: R20.2, T1.3 (RD+)
TXN: R17.2, T1.2 (TD-)
TXP: R18.2, T1.1 (TD+)
