ozcanyardimci/IoT_gateway/hardware/kicad/lteboard/lteboard/lte.kicad_sch

## KiCad design hardware/kicad/lteboard/lteboard/lte.kicad_sch (2026-09-19)

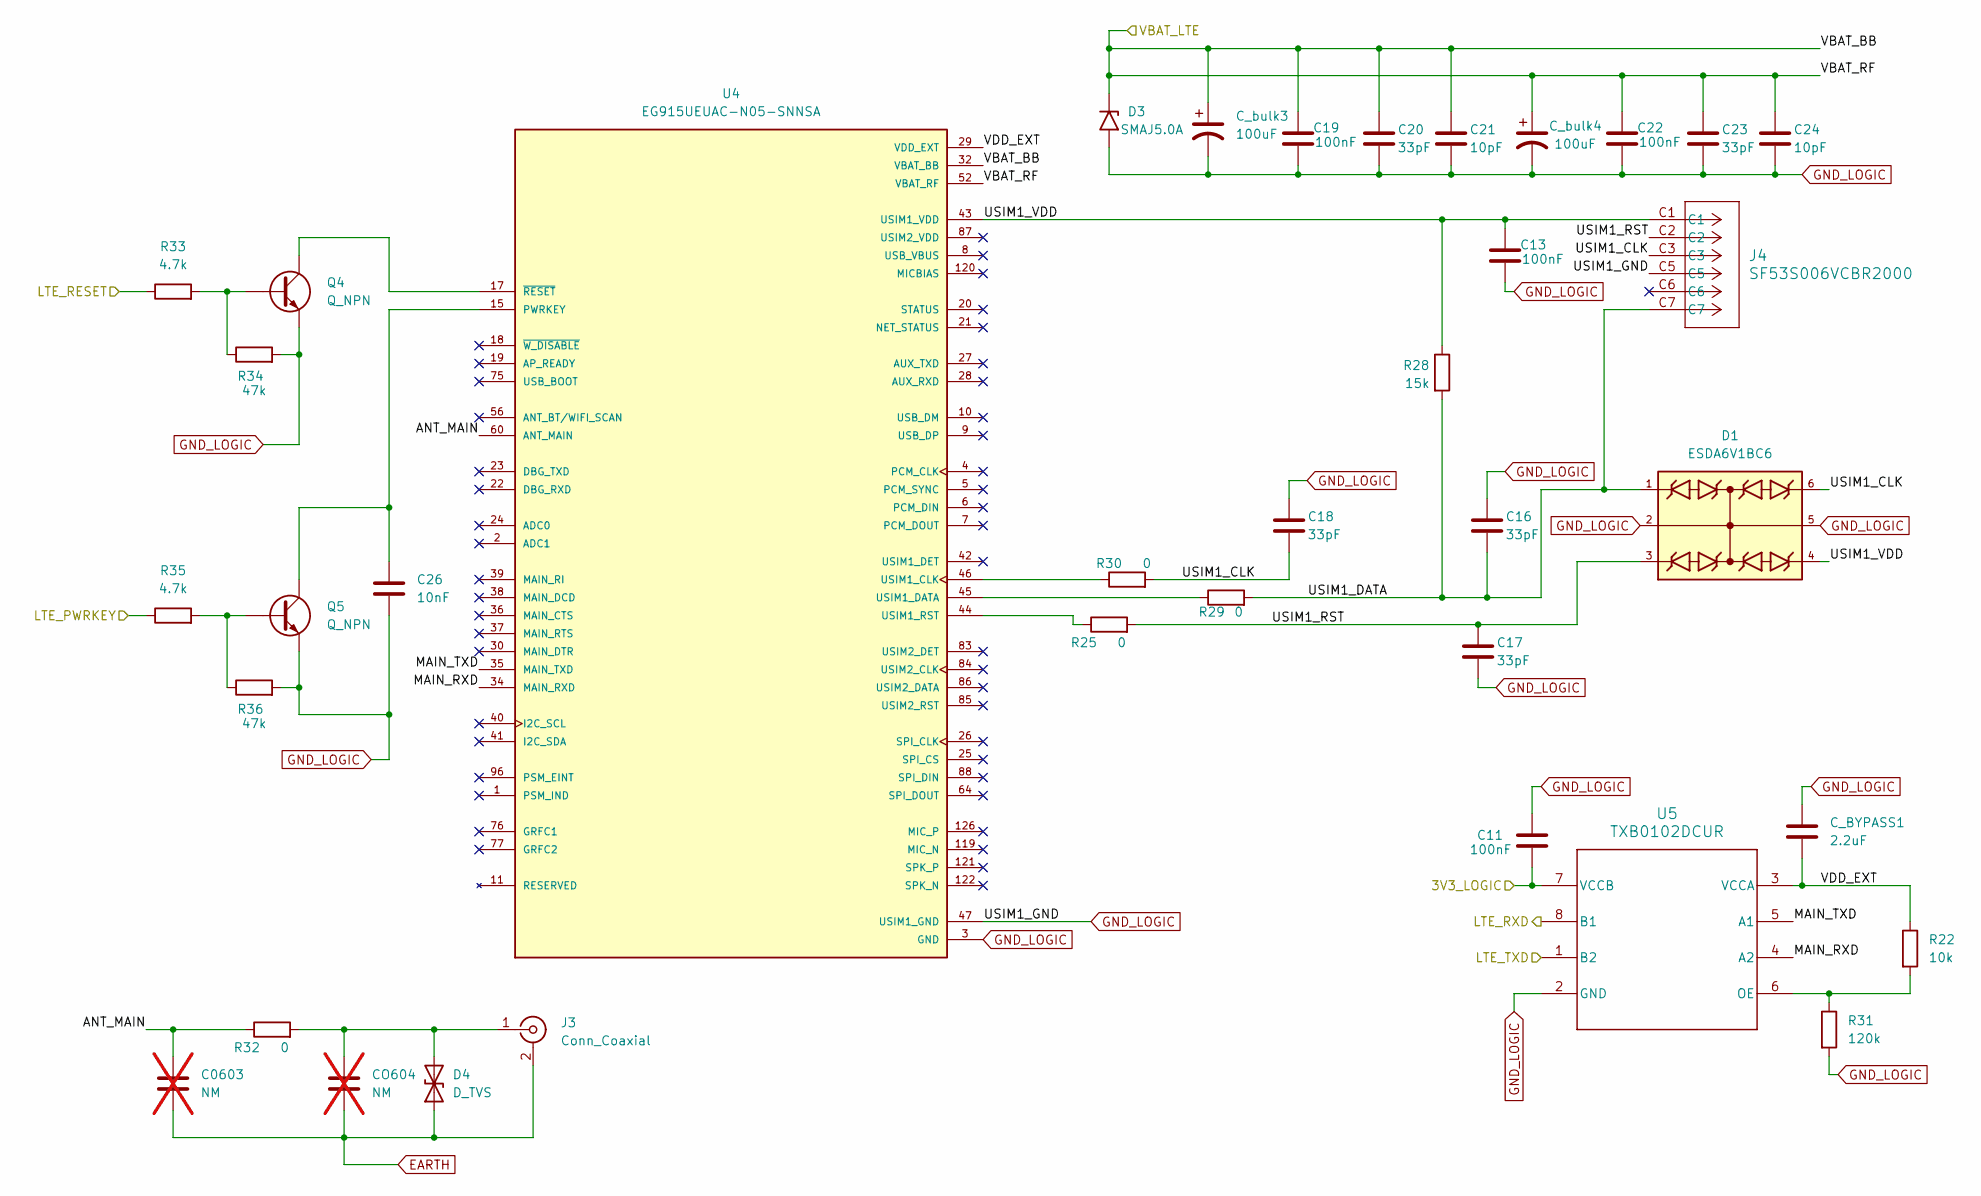
[picture p45: schematic lte.kicad_sch]

Parts:
C11, C13, C19, C22: 100nF
C16, C17, C18, C20, C23: 33pF
C21, C24: 10pF
C26: 10nF
C0603: NM; not fitted
CO604: NM; not fitted
C_BYPASS1: 2.2uF
C_bulk3, C_bulk4: 100uF
D1: ESDA6V1BC6; SOT95P280X145-6N; PARTREV 2
D3: SMAJ5.0A; D_SMA
D4: D_TVS
J3: Conn_Coaxial
J4: SF53S006VCBR2000; CONN_SF53S006VCBR2000_JAE
Q4, Q5: Q_NPN
R22: 10k
R25, R29, R30, R32: 0
R28: 15k
R31: 120k
R33, R35: 4.7k
R34, R36: 47k
U4: EG915UEUAC-N05-SNNSA; XCVR_EG915UEUAC-N05-SNNSA
U5: TXB0102DCUR; DCU0008A_N

Connections:
3V3_LOGIC: C11.2, U5.7 (VCCB)
ANT_MAIN: C0603.1, R32.1, U4.60 (ANT_MAIN)
EARTH: C0603.2, CO604.2, D4.1 (A1), J3.2 (Ext)
GND_LOGIC: C11.1, C13.2, C16.1, C17.2, C18.1, C19.2, C20.2, C21.2, C22.2, C23.2, C24.2, C26.2, C_BYPASS1.1, C_bulk3.2, C_bulk4.2, D1.2, D1.5, D3.2 (A2), J4.C5, Q4.E, Q5.E, R31.2, R34.2, R36.2, U4.3 (GND), U4.31 (GND), U4.47 (USIM1_GND), U4.48 (GND), U4.50 (GND), U4.54 (GND), U4.55 (GND), U4.58 (GND), U4.59 (GND), U4.61 (GND), U4.62 (GND), U4.67 (GND), U4.68 (GND), U4.69 (GND), U4.70 (GND), U4.71 (GND), U4.72 (GND), U4.73 (GND), U4.74 (GND), U4.79 (GND), U4.80 (GND), U4.81 (GND), U4.82 (GND), U4.89 (GND), U4.90 (GND), U4.91 (GND), U4.100 (GND), U4.101 (GND), U4.102 (GND), U5.2 (GND)
LTE_PWRKEY: R35.1
LTE_RESET: R33.1
LTE_RXD: U5.8 (B1)
LTE_TXD: U5.1 (B2)
MAIN_RXD: U4.34 (MAIN_RXD), U5.4 (A2)
MAIN_TXD: U4.35 (MAIN_TXD), U5.5 (A1)
unnamed: C26.1, Q5.C, U4.15 (PWRKEY)
unnamed: CO604.1, D4.2 (A2), J3.1 (In), R32.2
unnamed: Q4.B, R33.2, R34.1
unnamed: Q4.C, U4.17 (~RESET)
unnamed: Q5.B, R35.2, R36.1
unnamed: R22.2, R31.1, U5.6 (OE)
unnamed: R25.1, U4.44 (USIM1_RST)
unnamed: R29.1, U4.45 (USIM1_DATA)
unnamed: R30.1, U4.46 (USIM1_CLK)
unnamed: U4.11 (RESERVED), U4.12 (RESERVED), U4.13 (RESERVED), U4.14 (RESERVED), U4.16 (RESERVED), U4.49 (RESERVED), U4.51 (RESERVED), U4.57 (RESERVED), U4.63 (RESERVED), U4.65 (RESERVED), U4.66 (RESERVED), U4.78 (RESERVED), U4.92 (RESERVED), U4.93 (RESERVED), U4.94 (RESERVED), U4.95 (RESERVED), U4.97 (RESERVED), U4.98 (RESERVED), U4.99 (RESERVED), U4.103 (RESERVED), U4.104 (RESERVED), U4.105 (RESERVED), U4.106 (RESERVED), U4.107 (RESERVED), U4.108 (RESERVED), U4.109 (RESERVED), U4.110 (RESERVED), U4.111 (RESERVED), U4.112 (RESERVED), U4.113 (RESERVED), U4.114 (RESERVED), U4.115 (RESERVED), U4.116 (RESERVED), U4.117 (RESERVED), U4.118 (RESERVED), U4.123 (RESERVED), U4.124 (RESERVED), U4.125 (RESERVED)
USIM1_CLK: C18.2, D1.6, J4.C3, R30.2
USIM1_DATA: C16.2, D1.1, J4.C7, R28.2, R29.2
USIM1_RST: C17.1, D1.3, J4.C2, R25.2
USIM1_VDD: C13.1, D1.4, J4.C1, R28.1, U4.43 (USIM1_VDD)
VBAT_BB: C19.1, C20.1, C21.1, C22.1, C23.1, C24.1, C_bulk3.1, C_bulk4.1, D3.1 (A1), U4.32 (VBAT_BB), U4.33 (VBAT_BB), U4.52 (VBAT_RF), U4.53 (VBAT_RF)
VDD_EXT: C_BYPASS1.2, R22.1, U4.29 (VDD_EXT), U5.3 (VCCA)
