ozcanyardimci/IoT_gateway/hardware/kicad/lteboard/lteboard/status_indication.kicad_sch

## KiCad design hardware/kicad/lteboard/lteboard/status_indication.kicad_sch (2026-09-13)

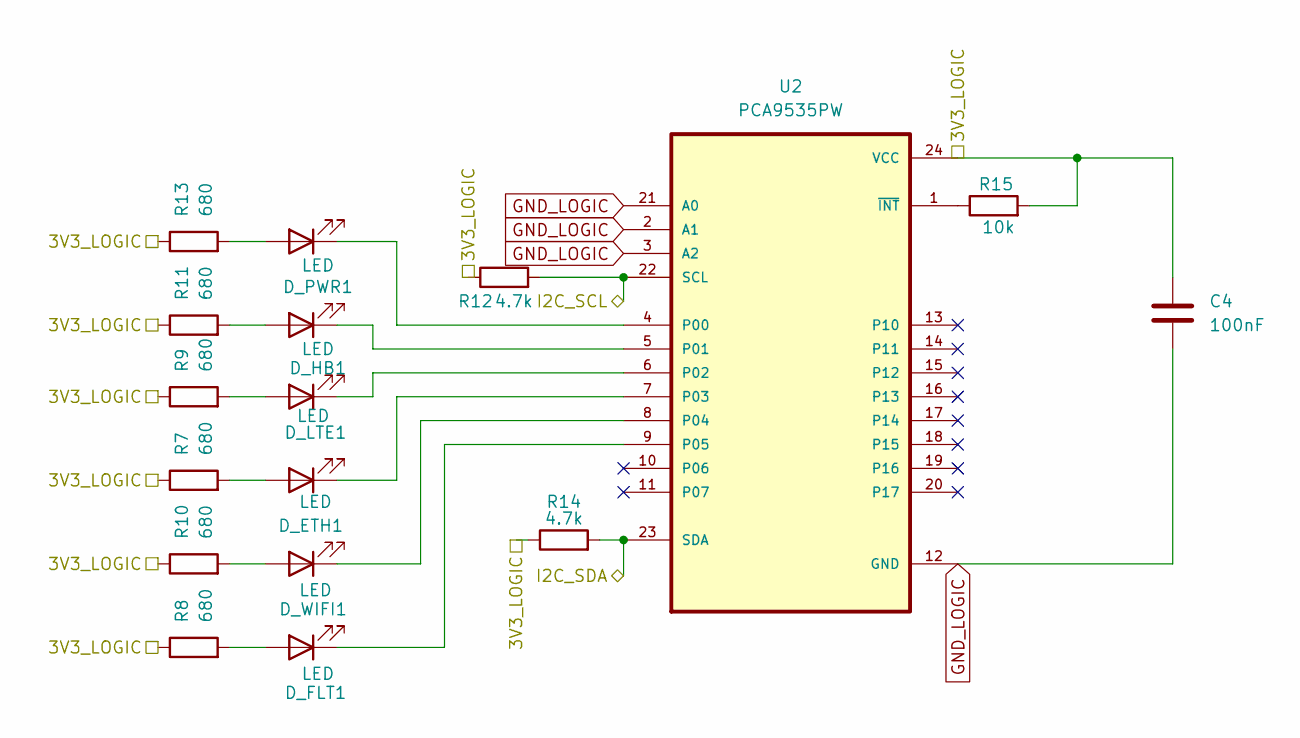
[picture p46: schematic status_indication.kicad_sch]

Parts:
C4: 100nF
D_ETH1: LED
D_FLT1: LED
D_HB1: LED
D_LTE1: LED
D_PWR1: LED
D_WIFI1: LED
R7, R8, R9, R10, R11, R13: 680
R12, R14: 4.7k
R15: 10k
U2: PCA9535PW; SOP65P640X120-24N

Connections:
3V3_LOGIC: C4.1, R7.1, R8.1, R9.1, R10.1, R11.1, R12.1, R13.1, R14.1, R15.2, U2.24 (VCC)
GND_LOGIC: C4.2, U2.2 (A1), U2.3 (A2), U2.12 (GND), U2.21 (A0)
I2C_SCL: R12.2, U2.22 (SCL)
I2C_SDA: R14.2, U2.23 (SDA)
unnamed: D_ETH1.1 (K), U2.7 (P03)
unnamed: D_ETH1.2 (A), R7.2
unnamed: D_FLT1.1 (K), U2.9 (P05)
unnamed: D_FLT1.2 (A), R8.2
unnamed: D_HB1.1 (K), U2.5 (P01)
unnamed: D_HB1.2 (A), R11.2
unnamed: D_LTE1.1 (K), U2.6 (P02)
unnamed: D_LTE1.2 (A), R9.2
unnamed: D_PWR1.1 (K), U2.4 (P00)
unnamed: D_PWR1.2 (A), R13.2
unnamed: D_WIFI1.1 (K), U2.8 (P04)
unnamed: D_WIFI1.2 (A), R10.2
unnamed: R15.1, U2.1 (~INT)
